DLehenbauer/econopet/docs/dev/PET/diagnostics.md

# Diagnostics

## Reference

* [cbm-burnin-tests](https://github.com/fachat/cbm-burnin-tests)
* [diagnostics.txt](https://www.zimmers.net/anonftp/pub/cbm/schematics/computers/pet/diagnostics.txt)
