DLehenbauer/econopet/docs/dev/timing.md

# Component Timing Reference

## W65C02S (CPU)

([Datasheet](https://www.westerndesigncenter.com/wdc/documentation/w65c02s.pdf))

| Symbol | Parameter | Min | Max | Units |
|---|---|-----|-----|---|
| tACC | Access Time |  70 | - | ns |
| tAH | Address Hold Time |  10 | - | ns |
| tADS | Address Setup Time | - |  40 | ns |
| tBVD | BE to Valid Data (1) | - |  30 | ns |
| tPWH | Clock Pulse Width High |  62 | - | ns |
| tPWL | Clock Pulse Width Low |  63 | - | ns |
| tCYC | Cycle Time (3) | 125 | - | ns |
| tF,tR  | Fall Time, Rise Time | - | 5 | ns |
| tPCH | Processor Control Hold Time |  10 | - | ns |
| tPCS | Processor Control Setup Time |  15 | - | ns |
| tDHR | Read Data Hold Time |  10 | - | ns |
| tDSR | Read Data Setup Time |  15 | - | ns |
| tMDS | Write Data Delay Time | - |  40 | ns |
| tDHW | Write Data Hold Time |  10 | - | ns |

Notes:

(1) BE to High Impedance State is not testable but should be the same amount of time as BE to Valid Data.

(3) Since this is a static design, the maximum cycle time could be infinite.

### Summary

Minimum Phi2 pulse width is high 62ns and low 63ns (tPWH, tPWL).

**Rising Phi2 edge triggers bus transfer:**

- BE must be asserted 45ns before rising Phi2 edge (tBVD + tDSR)
- DIN must be valid 15ns before rising Phi2 edge (tDSR)
- DIN must be held 10ns after rising Phi2 edge (tDHR)
- BE must be held 10ns after rising Phi2 edge (tDHR, tDHW)
- DOUT is valid within 40ns after rising Phi2 edge (tMDS)

**Falling Phi2 edge advances CPU to next state:**

- Previous ADDR, RWB, DOUT held 10ns after falling Phi2 edge (tAH, tDHW)
- Next ADDR, RWB, DOUT must be stable at least 40ns *before* the next rising Phi2 edge (tADS)
- Write data becomes valid within 40ns *after* that rising edge (tMDS)

**Other (design-derived):**

- At maximum clock rate, RAM has 70ns between ADDR stabilizing and the beginning of the read setup time (tACC).

## Soft-CPU Bus Timing

The physical PIA and VIA use `cpu_clock_o` as PHI2. The soft CPUs use separate
fabric clocks so their bus state does not advance until after the external
peripherals have observed falling PHI2 and completed their hold interval.

Within the 64-cycle, 64MHz arbiter frame:

| Event | Arbiter cycle | Purpose |
|---|---:|---|
| External PHI2 rises | 52 | Starts the physical peripheral transfer |
| CPU data strobe | 55 | External read or write data is guaranteed valid |
| External PHI2 falls | 60 | PIA and VIA latch the transfer |
| Soft 6809 Q falls | 60 | Samples synchronized interrupt inputs |
| Soft 6502 clock and 6809 E fall | 61 | Advances the selected soft CPU |

The 15.625ns interval from external PHI2 falling at cycle 60 to the soft-CPU
falling edge at cycle 61 exceeds the VIA's worst-case 10ns hold requirement.
Consequently, soft-CPU address, R/W, and write data remain stable without
adding bus latches.

`cpu_data_strobe` is itself registered. `main.sv` observes it on the following
system-clock edge, captures `cpu_data_q` for system-clock consumers, and raises
the delayed consumer strobe. That pulse also clocks `soft_cpu_data_q`, an
independent copy used only by the soft cores. This gives external data one
system-clock period to reach both capture registers. The soft-core copy remains
stable for five more system cycles before the selected core falls.

`EconoPET.sdc` models the short soft-core pulses with explicit generated-clock
edges. The first rising edge processes the initial `cycle_count` value 63, so
arbiter cycle 0 is processed on the second rising edge. SDC numbers every
source-clock transition (rise 1, fall 2, next rise 3), so arbiter cycle N
corresponds to source edge `2N+3`. The SDC also constrains the pin-to-capture
path to one system period. The delayed `cpu_data_strobe_q` pulse directly clocks
`soft_cpu_data_q` at cycle 56 and is declared as its generated launch clock.
STA can therefore derive the five-cycle setup and full-frame hold relationships
without a data-path exception. Keeping `cpu_data_q` on `sys_clock_i` separately
gives its consumers an ordinary one-cycle relationship. Remaining hold
adjustments are limited to edge-elastic READY/interrupt controls. The 6809's
IRQ sample register provides the first Q-domain synchronizer stage.

## W65C21N (PIA)

([Datasheet](https://www.westerndesigncenter.com/wdc/documentation/w65c21.pdf))

| Symbol | Parameter | Min | Max | Units |
|---|---|-----|-----|---|
| tCYC | PHI2 Cycle |  70 | - | ns |
| tC | PHI2 Pulse Width |  35 | - | ns |
| trc | PHI2 Rise Time | - | 5 | ns |
| tfc | PHI2 Fall Time | - | 5 | ns |
| tACR | Address Set-Up Time (read) | 8 | - | ns |
| tCAR | Address Hold Time (read) | 0 | - | ns |
| tPCR | Peripheral Data Setup Time |  10 | - | ns |
| tCDR | Data Bus Delay Time | - |  20 | ns |
| tHR | Data Bus Hold Time | 5 | - | ns |
| tACW | Address Set-Up Time (write) | 8 | - | ns |
| tCAW | Address Hold Time (write) | 0 | - | ns |
| tDCW | Data Bus Set-Up Time |  10 | - | ns |
| tHW | Data Bus Hold Time | 5 | - | ns |
| tCPW | Peripheral Data Delay Time | - |  20 | ns |

### Summary

- Minimum Phi2 pulse width is high 35ns and low 35ns (tCYC, tC)
- ADDR, RWD, CS2B must be stable at least 8ns before rising Phi2 (tACR, tACW) and may be released 0ns after falling Phi2 (tCAR, tCAW)
- Peripheral read data becomes valid within 20ns after rising Phi2 (tCDR) and is held 5ns after falling Phi2 (tHR)
- Peripheral write data must be set up 10ns before falling Phi2 (tDCW) and held 5ns after falling Phi2 (tHW)
- Peripheral-side data can appear within 20ns after rising Phi2 (tCPW)

## W65C22N (VIA)

([Datasheet](https://www.westerndesigncenter.com/wdc/documentation/w65c22.pdf))

| Symbol | Parameter | Min | Max | Units |
|---|---|-----|-----|---|
| tCYC | Cycle Time |  70 | - | ns |
| tPWH | Phase 2 Pulse Width High |  35 | - | ns |
| tPWL | Phase 2 Pulse Width Low |  35 | - | ns |
| tR,F | Phase 2 Transition | - | 5 | ns |
| tACR | CSx, RSx, RWB Setup - READ |  10 | - | ns |
| tCAR | CSx, RSx, RWB Hold (PHI2 falling edge) - READ |  10 | - | ns |
| tCDR | Data Bus Delay | - |  20 | ns |
| tHR | Data Bus Hold Time |  10 | - | ns |
| tPCR | Peripheral Data Setup |  10 | - | ns |
| tACW | CSx, RSx, RWB Setup - WRITE |  10 | - | ns |
| tCAW | CSx, RSx, RWB Hold (PHI2 falling edge) - WRITE | 10 | - | ns |
| tDCW | Data Bus Setup |  10 | - | ns |
| tHW | Data Bus Hold |  10 | - | ns |
| tCPW | Peripheral Data Delay | - | 250 | ns |

### Summary

- Minimum Phi2 pulse width is high 35ns and low 35ns (tPWH, tPWL)
- ADDR/CSx/RSx/RWB must be stable at least 10ns before rising Phi2 (tACR, tACW) and held 10ns after falling Phi2 (tCAR, tCAW).
- Peripheral read data becomes valid within 20ns after rising Phi2 (tCDR) and is held 10ns after falling Phi2 (tHR).
- Peripheral write data must be set up 10ns before falling Phi2 (tDCW) and held 10ns after falling Phi2 (tHW).
- Peripheral-side data can appear within ~250ns after rising Phi2 (tCPW).

## SN74LVC4245A (Level Shifter)

([Datasheet](https://www.ti.com/lit/ds/symlink/sn74lvc4245a.pdf))

Two SN74LVC4245A devices provide level shifting between the CPU and PIA/VIA:

- Address A0-A3: fixed direction from CPU to PIA/VIA (B to A), permanently enabled.
- Data D0-D7: bidirectional. DIR follows CPU RWB (read: A to B, write: B to A). /OE is asserted by the FPGA during decoded PIA/VIA accesses; otherwise the device is high-Z to avoid contention.

The timing values below bound propagation and enable/disable delays used when budgeting setup/hold margins for CPU-to-PIA/VIA transfers.

| Symbol | From | To | Min | Max  | Units |
|---|---|----|-----|---|---|
| tPHL | A | B  | 1 |  6.3 | ns |
| tPLH | A | B  | 1 |  6.7 | ns |
| tPHL | B | A  | 1 |  6.1 | ns |
| tPLH | B | A  | 1 |  5.0 | ns |
| tPZL | /OE  | A  | 1 |  9.0 | ns |
| tPZH | /OE  | A  | 1 | 10.0 | ns |
| tPZL | /OE  | B  | 1 | 10.3 | ns |
| tPZH | /OE  | B  | 1 |  9.8 | ns |
| tPLZ | /OE  | A  | 1 |  7.0 | ns |
| tPHZ | /OE  | B  | 1 |  5.8 | ns |
| tPLZ | /OE  | B  | 1 |  7.7 | ns |
| tPHZ | /OE  | B  | 1 |  7.8 | ns |

### Summary

- Propagation: A to B up to 6.7ns (tPLH A to B); B to A up to 6.1ns (tPHL B to A). Budget 6.7ns worst-case.
- Enable (/OE asserted): to B up to 10.3ns (tPZL /OE to B); to A up to 10.0ns (tPZH /OE to A).
- Disable (/OE deasserted): to B high-Z up to 7.8ns (tPHZ /OE to B); to A high-Z up to 7.0ns (tPLZ /OE to A). Budget 7.8ns worst-case.
- Turn-around: deassert /OE, wait >=7.8ns to reach high-Z, switch DIR, then re-assert /OE to avoid contention.

## AS6C1008-55PCN (SRAM)

([Datasheet](https://www.alliancememory.com/wp-content/uploads/AS6C1008_Mar_2023V1.2.pdf))

### Read Cycle

| Symbol | Parameter | Min | Max | Units |
|---|---|-----|-----|---|
| tRC | Read Cycle Time |  55 | - | ns |
| tAA | Address Access Time | - |  55 | ns |
| tACE | Chip Enable Access Time | - |  55 | ns |
| tOE | Output Enable Access Time | - |  30 | ns |
| tCLZ | Chip Enable to Output in Low-Z | - |  10 | ns |
| tOLZ | Output Enable to Output in Low-Z | - | 5 | ns |
| tCHZ | Chip Disable to Output in High-Z | - |  20 | ns |
| tOHZ | Output Disable to Output in High-Z | - |  20 | ns |
| tOH | Output Hold from Address Change |  10 | - | ns |

### Write Cycle

| Symbol | Parameter | Min | Max | Units |
|---|---|-----|-----|---|
| tWC | Write Cycle Time |  55 | - | ns |
| tAW | Address Valid to End of Write |  50 | - | ns |
| tAS | Address Setup Time | 0 | - | ns |
| tWP | Write Pulse Width |  45 | - | ns |
| tWR | Write Recovery Time | 0 | - | ns |
| tDW | Data to Write Time Overlap |  25 | - | ns |
| tDH | Data Hold from End of Write Time | 0 | - | ns |
| tOW | Output Active from End of Write | 5 | - | ns |
| tWHZ | Write to Output in High-Z | - |  20 | ns |

### Summary

- DOUT valid 55ns after coincident ADDR and OE: max(tAA, tOE, tOLZ).
- DOUT held 10ns after ADDR changes (tOH).
- DOUT returns to High-Z 20ns after OE deasserted (tOHZ).
- CE is permanently asserted, so tACE, tCLZ, tCHZ, and tCW are not relevant.
- Total write cycle time must be at least 55ns (tWC).
- ADDR must be valid 50ns before WE deasserts; no hold requirement (tAW, tWR = 0ns).
- DIN must be valid 25ns before WE deasserts; no hold requirement (tDW, tDH = 0ns).
- WE pulse width must be at least 45ns (tWP).
- OE is deasserted during writes, so tOW and tWHZ are not relevant.

## IS61WV1288EEBLL-10TLI (SRAM)

### Read Cycle

| Symbol | Parameter | Min | Max | Units |
|---|---|-----|-----|---|
| tRC | Read Cycle Time |  10 |  -  | ns |
| tAA | Address Access Time | - |  10 | ns |
| tOHA | Output Hold Time | 2.0 |  -  | ns |
| tACE | $\overline{CE}$ Access Time | - |  10 | ns |
| tDOE | $\overline{OE}$ Access Time | - | 4.5 | ns |
| tHZOE  | $\overline{OE}$ to High-Z Output | - | 4 | ns |
| tLZOE  | $\overline{OE}$ to Low-Z Output  | 0 | - | ns |
| tHZCE  | $\overline{CE}$ to High-Z Output | 0 | 4 | ns |
| tLZCE  | $\overline{CE}$ to Low-Z Output  | 3 | - | ns |
| tPU | Power Up Time | 0 | - | ns |
| tPD | Power Down Time | - |  10 | ns |

### Write Cycle

| Symbol | Parameter | Min | Max | Units |
|---|---|-----|-----|---|
| tWC | Write Cycle Time |  10 | - | ns |
| tSCE | $\overline{CE}$ to Write End | 8 | - | ns |
| tAW | Address Setup Time to Write End | 8 | - | ns |
| tHA | Address Hold from Write End | 0 | - | ns |
| tSA | Address Setup Time | 0 | - | ns |
| tPWE1  | $\overline{WE}$ Pulse Width | 8 | - | ns |
| tPWE2  | $\overline{WE}$ Pulse Width ($\overline{OE}$ = LOW) |  10 | - | ns |
| tSD | Data Setup to Write End | 6 | - | ns |
| tHD | Data Hold from Write End | 0 | - | ns |
| tHZWE  | $\overline{WE}$ LOW to High-Z Output | - | 5 | ns |
| tLZWE  | $\overline{WE}$ HIGH to Low-Z Output | 2 | - | ns |

### Summary

- DOUT valid 10ns after coincident ADDR and $\overline{CE}$ (tAA, tACE).
- DOUT valid 4.5ns after $\overline{OE}$ asserted (tDOE).
- DOUT held 2.0ns after ADDR changes (tOHA).
- DOUT returns to High-Z 4ns after $\overline{OE}$ or $\overline{CE}$ deasserted (tHZOE, tHZCE).
- Total write cycle time must be at least 10ns (tWC).
- ADDR must be valid 8ns before $\overline{WE}$ or $\overline{CE}$ deasserts (tAW).
- ADDR must be set up 0ns before $\overline{WE}$ or $\overline{CE}$ asserts (tSA).
- ADDR must be held 0ns after $\overline{WE}$ or $\overline{CE}$ deasserts (tHA).
- DIN must be valid 6ns before $\overline{WE}$ or $\overline{CE}$ deasserts (tSD).
- DIN must be held 0ns after $\overline{WE}$ or $\overline{CE}$ deasserts (tHD).
- $\overline{WE}$ pulse width must be at least 8ns (tPWE1) or 10ns if $\overline{OE}$ is LOW (tPWE2).
- $\overline{CE}$ must be asserted for at least 8ns before write end (tSCE).
