DLehenbauer/econopet/docs/dev/PET/roms.md

# ROMs

## Naming

 Common         | Geneology      | Generation | Level
----------------|----------------|------------|-----------------
 BASIC 1.0      | ROM 1.0        | Original   | Basic Level I
 BASIC 1.0R     | ROM 2.0        | Original   | Basic Level II  
 BASIC 2.0      | ROM 3.0        | Upgrade    | Basic Level III
 BASIC 4.0      | ROM 4.0        | 4.0        | Basic Level IV
 BASIC 4.0R     | ROM 4.1        | 4.0        | Basic Level IV

* [ROM Genealogy](http://penguincentral.com/retrocomputing/PET/petroms.pdf) is official Commodore documentation preserved by Ethan Dicks
* [ROM Genealogy](https://archive.org/details/commodore-newsletter-volume-1-number-10/page/31/mode/1up) is a subset of the above from Commodore Newsletter Vol 1, No 10 (1982)
* Jim Butterfield's [What Software Do I Have?](https://archive.org/details/cbm_magazine_index-interface/interface/1981/interface-13-198107/page/n10/mode/1up) article in Interface Magazine (July 1981)

## ROM 1.0

Early production PET 2001 units used MOS 6540 ROMs (28-pin).  Later revisions used 2316 ROMs (24-pin).

The 28-pin and 24-pin ROMs have different IC and part numbers, but their contents are identical.

Highlights:

* Arrays limited to 256 items
* IEEE-488 input not working
* Tape data files had potential problems
* No machine language monitor
* Screen output polls for vertical refresh to avoid "sparkle" (see [killerpoke.md](killerpoke.md))

Address | Location | 6540 IC# | 6540 Part# | 2316B IC# | 2316B Part# | CRC-32   | Checksum
--------|----------|----------|------------|-----------|-------------|----------|---------
  $C000 |    H1    | 6540-011 |  901439-01 | 2316B-01  |  901447-01  | a055e33a | AD?
  $D000 |    H2    | 6540-013 |  901439-02 | 2316B-03  |  901447-03  | d349f2d4 | 15?
  $E000 |    H3    | 6540-015 |  901439-03 | 2316B-05  |  901447-05  | 9e1c5cea | 60?
  $F000 |    H4    | 6540-016 |  901439-04 | 2316B-06  |  901447-06  | 661a814a | F5?
  $C800 |    H5    | 6540-012 |  901439-05 | 2316B-02  |  901447-02  | 69fd8a8f | 09?
  $D800 |    H6    | 6540-014 |  901439-06 | 2316B-04  |  901447-04  | 850544eb | 0E?
  $F800 |    H7    | 6540-018 |  901439-07 | 2316B-07  |  901447-07  | c4f47ad1 | 4A?
  N/A   |    A2    | 6540-010 |  901439-08 | 2316B-08  |  901447-08  | 54f32f45 | ?

### Keyboard (901447-05)

Graphics/QWERTY keyboard scanmap at $e75c:

```text
>C:e75c  3d 2e ff 03  3c 20 5b 12   =...< [.
>C:e764  2d 30 00 3e  ff 5d 40 00   -0.>.]@.
>C:e76c  2b 32 ff 3f  2c 4e 56 58   +2.?,NVX
>C:e774  33 31 0d 3b  4d 42 43 5a   31.;MBCZ
>C:e77c  2a 35 ff 3a  4b 48 46 53   *5.:KHFS
>C:e784  36 34 ff 4c  4a 47 44 41   64.LJGDA
>C:e78c  2f 38 ff 50  49 59 52 57   /8.PIYRW
>C:e794  39 37 5e 4f  55 54 45 51   97^OUTEQ
>C:e79c  14 11 ff 29  5c 27 24 22   ...)\'$"
>C:e7a4  1d 13 5f 28  26 25 23 21   .._(&%#!
```

### Vertical Refresh

To prevent sparkle, polls via VIA PB5 (pin 15) to wait for vertical refresh before writing to VRAM.

```txt
.C:e7ad  AD 40 E8    LDA $E840
.C:e7b0  29 20       AND #$20
.C:e7b2  D0 F9       BNE $E7AD
```

### Disk

There is a patch for H4 [here](https://hub.inktada.com/channel/rom1diskmagic) that fixes the issue with disk drives.

[Disassembly](https://www.zimmers.net/anonftp/pub/cbm/src/pet/rom-1.html)

## ROM 2.0

Highlights:

* Fixed bug limiting the dimensions of arrays.
* Corrects an intermittent bug in the edit software.
* Improves the garbage collection routines.

Identical to ROM 1.0 except H1 ($C000).

Address | Location | 6540 IC# | 6540 Part# | 2316B IC# | 2316B Part# | CRC-32   | Checksum
--------|----------|----------|------------|-----------|-------------|----------|---------
  $C000 | H1       | 6540-019 |  901439-09 | 2316B-09  |  901447-09  | 03cf16d0 | 19?

### PET 2001-8N (VICE)

The VICE roms are a binary concatenation of the ROMs indicated in the filenames:

ROM         | File                            | Length | CRC-32
------------|---------------------------------|--------|---------
Basic       | basic-1.901439-09-05-02-06.bin  |   8192 | aff78300
Edit        | edit-1-n.901439-03.bin          |   2048 | 9e1c5cea
Kernal      | kernal-1.901439-04-07.bin       |   4096 | f0186492
Characters  | characters-1.901447-08.bin      |   2048 | 54f32f45

## ROM 3.0

Highlights:

* Changed the banner ("***" -> "###")
* Fixed support for commodore disk system
* Adds machine language monitor
* Further improved garbage collection
* Re-arranged the zero-page and ROM entry points
* Adds ROM set for business keyboards
* New character ROM (swaps upper/lower case)
* Screen output polls for vertical refresh to avoid "sparkle" (see [killerpoke.md](killerpoke.md))

### PET 2001 / 30xx

The 24-pin BASIC and Kernal ROMs are 4KB.  The contents of H1-H3 are identical to the concatenation of H1/H5, H2/H6, H3/H7.
The 28-pin ROM upgrade set did not include a new character ROM.  Therefore, upper/lowercase continue to be swapped (like in BASIC 1-2).

Address | Location | 6540 IC# | 6540 Part# | CRC-32    | 2316B IC# | 2316B Part# | CRC-32   | Checksum
--------|----------|----------|------------|-----------|-----------|-------------|----------|---------
  $C000 | H1, D6   | 6540-020 |  901439-13 | 6aab64a5  |  2332-007 |   901465-01 | 63a7fe4a |    77
  $D000 | H2, D7   | 6540-022 |  901439-15 | 97f7396a  |  2332-008 |   901465-02 | ae4cb035 |    Cl
  $E000 | H3, D8   | 6540-024 |  901439-17 | e459ab32  | 2316B-011 |   901447-24 | e459ab32 |    C0
  $F000 | H4, D9   | 6540-025 |  901439-18 | 8745fc8a  |  2332-009 |   901465-03 | f02238e2 |    1D
  $C800 | H5       | 6540-021 |  901439-14 | a8f6ff4c  | -         |   -         | -        | -
  $D800 | H6       | 6540-023 |  901439-16 | 4cf8724c  | -         |   -         | -        | -
  $F800 | H7       | 6540-026 |  901439-19 | fd2c1f87  | -         |   -         | -        | -
  N/A   | A2, F10  | 6540-010 |  901439-08 | 54f32f45  | 2316B-004 |   901447-10 | d8408674 | ?

### PET 30xxB (Business Keyboard)

Business keyboard is identical except for editor ROM (D8).

Address | Location | IC#       | Part#     | CRC-32   | Checksum
--------|----------|-----------|-----------|----------|---------
  $E000 | D8       |2316B-024  | 901474-01 | 05db957e |    F3

### Scanmap (901474-01)

Business/QWERTY keyboard scanmap at $e6fb:

```text
>C:e6fb  50 e7 3a 03  39 36 33 df   P.:.963.
>C:e703  b1 2f ff 13  4d 20 58 12   ./..M X.
>C:e70b  b2 ff ff b0  2c 4e 56 5a   ....,NVZ
>C:e713  b3 00 ff ae  2e 42 43 00   .....BC.
>C:e71b  b4 db 4f 11  55 54 45 51   ..O.UTEQ
>C:e723  14 50 49 dc  59 52 57 89   .PI.YRW.
>C:e72b  b6 c0 4c 0d  4a 47 44 41   ..L.JGDA
>C:e733  b5 3b 4b dd  48 46 53 9b   .;K.HFS.
>C:e73b  b9 ff de b7  b0 37 34 31   .....741
>C:e743  ff ff 1d b8  2d 38 35 32   ....-852
```

Note that the first two table entries are an instruction. Presumably these keys are unpressable? (CTRL-V, CTRL-D)

```text
.C:e6fb  50 E7       BVC $E6E4
```

### PET 30xx (VICE)

The VICE roms are a binary concatenation of the ROMs indicated in the filenames:

ROM         | File                            | Length | CRC-32  
------------|---------------------------------|--------|---------
Basic       | basic-2.901465-01-02.bin        |   8192 | cf35e68b
Edit        | edit-2-n.901447-24.bin          |   2048 | e459ab32
Kernal      | kernal-2.901465-03.bin          |   4096 | f02238e2
Characters  | characters-2.901447-10.bin      |   2048 | d8408674

Business keyboard is identical to 30XX except for Edit rom.

ROM         | File                            | Length | CRC-32  
------------|---------------------------------|--------|---------
Edit        | edit-2-b.901474-01.bin          |   2048 | 05db957e

## ROM 4.0

Highlights:

* Added the disk commands and status variables
* Greatly improved the garbage collection
* Adds ROM set for 80 column displays

### PET 2001 & 40XX (Graphics Keyboard, NoCRTC)

Address | Location | IC#       | Part#     | CRC-32   | Checksum
--------|----------|-----------|-----------|----------|---------
  $9000 | D3       | -         | -         | -        | -
  $A000 | D4       | -         | -         | -        | -
  $B000 | D5       |  2332     | 901465-19 | 3a5f5721 |    B1?
  $C000 | D6       |  2332-059 | 901465-20 | 0fc17b9c |    C0
  $D000 | D7       |  2332-096 | 901465-21 | 36d91855 |    D0
  $E000 | D8       | 2316B-034 | 901447-29 | e5714d4c |    E0
  $F000 | D9       |  2332-075 | 901465-22 | cc5298a1 |    F0
  N/A   | F10      | 2316B-004 | 901447-10 | d8408674 | ?

### PET 2001 & 40XX (Business Keyboard, NoCRTC)

Business keyboard is identical except for D8.

Address | Location | IC#       | Part#     | CRC-32   | Checksum
--------|----------|-----------|-----------|----------|---------
  $E000 | D8       | 2316B-035 | 901474-02 | 75ff4af7 |    E0

### PET 40XX (CRTC, 60 Hz)

Same ICs as NoCRTC except UD7.

Address | Location | IC#       | Part#     | CRC-32   | Checksum
--------|----------|-----------|-----------|----------|---------
  $F000 | UD6      |  2332-075 | 901465-22 | cc5298a1 |    F0
  $E000 | UD7      |  2316B    | 901499-01 | 5f85bdf8 |    BC
  $D000 | UD8      |  2332-096 | 901465-21 | 36d91855 |    D0
  $C000 | UD9      |  2332-059 | 901465-20 | 0fc17b9c |    C0
  $B000 | UD10     |  2332     | 901465-19 | 3a5f5721 | ?
  $A000 | UD11     | -         | -         | -        | -
  $9000 | UD12     | -         | -         | -        | -
  N/A   | F10      | 2316B-004 | 901447-10 | d8408674 | ?

#### Graphics Scanmap (901498-01, 901499-01)

```text
>C:e73f  3d 2e 10 03  3c 20 5b 12   =...< [.
>C:e747  2d 30 00 3e  ff 5d 40 00   -0.>.]@.
>C:e74f  2b 32 ff 3f  2c 4e 56 58   +2.?,NVX
>C:e757  33 31 0d 3b  4d 42 43 5a   31.;MBCZ
>C:e75f  2a 35 ff 3a  4b 48 46 53   *5.:KHFS
>C:e767  36 34 ff 4c  4a 47 44 41   64.LJGDA
>C:e76f  2f 38 ff 50  49 59 52 57   /8.PIYRW
>C:e777  39 37 5e 4f  55 54 45 51   97^OUTEQ
>C:e77f  14 11 09 29  5c 27 24 22   ...)\'$"
>C:e787  1d 13 5f 28  26 25 23 21   .._(&%#!
```

#### CRTC Tables (901499-01)

Text Mode
```
>C:e7b1  31 28 29 0f  20 03 19 1d   1(). ...
>C:e7b9  00 09 00 00  10 00 00 00   ........
>C:e7c1  00 00                      ..
```

Graphics Mode
```
>C:e7c3  31 28 29 0f  28 05 19 21   1().(..!
>C:e7cb  00 07 00 00  10 00 00 00   ........
>C:e7d3  00 00                      ..
```

### PET 40XXB (CRTC, 60Hz, Business)

Business keyboard is identical to 40XX except for Edit rom.

ROM         | File                            | Length | CRC-32  
------------|---------------------------------|--------|---------
Edit        | edit-4-40-b-60Hz.ts.bin         |   2048 | 7a0e59ad

Below are the edit rom changes required for the business keyboard:

```patch
- .C:e55c  EA          NOP
- .C:e55d  EA          NOP
- .C:e55e  EA          NOP
- .C:e55f  EA          NOP
- .C:e560  EA          NOP
- .C:e561  EA          NOP
- .C:e562  EA          NOP
+ .C:e55c  AA          TAX
+ .C:e55d  08          PHP
+ .C:e55e  29 7F       AND #$7F
+ .C:e560  28          PLP
+ .C:e561  30 17       BMI $E57A
.C:e563  46 98       LSR $98
.C:e565  90 13       BCC $E57A
- .C:e567  EA          NOP
- .C:e568  EA          NOP
- .C:e569  EA          NOP
- .C:e56a  EA          NOP
- .C:e56b  EA          NOP
- .C:e56c  EA          NOP
- .C:e56d  EA          NOP
- .C:e56e  EA          NOP
- .C:e56f  EA          NOP
- .C:e570  EA          NOP
- .C:e571  EA          NOP
- .C:e572  EA          NOP
- .C:e573  EA          NOP
- .C:e574  EA          NOP
- .C:e575  EA          NOP
- .C:e576  EA          NOP
- .C:e577  EA          NOP
+ .C:e567  C9 2C       CMP #$2C
+ .C:e569  90 0D       BCC $E578
+ .C:e56b  C9 3C       CMP #$3C
+ .C:e56d  B0 09       BCS $E578
+ .C:e56f  E9 0F       SBC #$0F
+ .C:e571  C9 20       CMP #$20
+ .C:e573  B0 05       BCS $E57A
+ .C:e575  69 20       ADC #$20
+ .C:e577  2C 09 80    BIT $8009
```

```text
>C:e73f  16 04 3a 03  39 36 33 df   ..:.963.
>C:e747  b1 2f 15 13  4d 20 58 12   ./..M X.
>C:e74f  b2 10 0f b0  2c 4e 56 5a   ....,NVZ
>C:e757  b3 00 19 ae  2e 42 43 00   .....BC.
>C:e75f  b4 db 4f 11  55 54 45 51   ..O.UTEQ
>C:e767  14 50 49 dc  59 52 57 09   .PI.YRW.
>C:e76f  b6 c0 4c 0d  4a 47 44 41   ..L.JGDA
>C:e777  b5 3b 4b dd  48 46 53 9b   .;K.HFS.
>C:e77f  b9 06 de b7  b0 37 34 31   .....741
>C:e787  05 0e 1d b8  2d 38 35 32   ....-852
```

### PET 40XX (CRTC, 50Hz)

Identical except for UD7.  Scanmap at $e73f.

Address | Location | IC#       | Part#     | CRC-32   | Checksum
--------|----------|-----------|-----------|----------|---------
  $E000 | UD7      | 2316B     | 901498-01 | 3370e359 | ?

Below are the edit rom changes for 50 Hz.

```patch
- e455  20 ea ff   JSR UDTIM
+ e455  4c 2e e4   JMP $e42e
```

```patch
- e7b5  20         db 20h
+ e7b5  27         db 27h
- e7b6  03         db 3h
+ e7b6  00         db 0h
  e7b7  19         db 19h
- e7b8  1d         db 1Dh
+ e7b8  20         db 20h

- e7c7  28         db 28h
+ e7c7  31         db 31h
- e7c8  05         db 5h
+ e7c8  00         db 0h
  e7c9  19         db 19h
- e7ca  21         db 21h
+ e7ca  25         db 25h
```

```patch
- e7e4  bb         db BBh
+ e7e4  29         db 29h
```

#### CRTC Tables (901498-01)

Text Mode
```
>C:e7b1  31 28 29 0f  27 00 19 20   1().'.. 
>C:e7b9  00 09 00 00  10 00 00 00   ........
>C:e7c1  00 00
```

Graphics Mode
```
>C:e7c3  31 28 29 0f  31 00 19 25   1().1..%
>C:e7cb  00 07 00 00  10 00 00 00   ........
>C:e7d3  00 00                      ..
```

### PET 40XXB (CRTC, 50Hz, Business)

Business keyboard is identical to 40XX except for Edit rom.

ROM         | File                            | Length | CRC-32  
------------|---------------------------------|--------|---------
Edit        | edit-4-40-b-50Hz.ts.bin         |   2048 | 16fb070c

Below are the edit rom changes required for the business keyboard:

```patch
- .C:e55c  EA          NOP
- .C:e55d  EA          NOP
- .C:e55e  EA          NOP
- .C:e55f  EA          NOP
- .C:e560  EA          NOP
- .C:e561  EA          NOP
- .C:e562  EA          NOP
+ .C:e55c  AA          TAX
+ .C:e55d  08          PHP
+ .C:e55e  29 7F       AND #$7F
+ .C:e560  28          PLP
+ .C:e561  30 17       BMI $E57A
.C:e563  46 98       LSR $98
.C:e565  90 13       BCC $E57A
- .C:e567  EA          NOP
- .C:e568  EA          NOP
- .C:e569  EA          NOP
- .C:e56a  EA          NOP
- .C:e56b  EA          NOP
- .C:e56c  EA          NOP
- .C:e56d  EA          NOP
- .C:e56e  EA          NOP
- .C:e56f  EA          NOP
- .C:e570  EA          NOP
- .C:e571  EA          NOP
- .C:e572  EA          NOP
- .C:e573  EA          NOP
- .C:e574  EA          NOP
- .C:e575  EA          NOP
- .C:e576  EA          NOP
- .C:e577  EA          NOP
+ .C:e567  C9 2C       CMP #$2C
+ .C:e569  90 0D       BCC $E578
+ .C:e56b  C9 3C       CMP #$3C
+ .C:e56d  B0 09       BCS $E578
+ .C:e56f  E9 0F       SBC #$0F
+ .C:e571  C9 20       CMP #$20
+ .C:e573  B0 05       BCS $E57A
+ .C:e575  69 20       ADC #$20
+ .C:e577  2C 09 80    BIT $8009
```

```text
>C:e73f  16 04 3a 03  39 36 33 df   ..:.963.
>C:e747  b1 2f 15 13  4d 20 58 12   ./..M X.
>C:e74f  b2 10 0f b0  2c 4e 56 5a   ....,NVZ
>C:e757  b3 00 19 ae  2e 42 43 00   .....BC.
>C:e75f  b4 db 4f 11  55 54 45 51   ..O.UTEQ
>C:e767  14 50 49 dc  59 52 57 09   .PI.YRW.
>C:e76f  b6 c0 4c 0d  4a 47 44 41   ..L.JGDA
>C:e777  b5 3b 4b dd  48 46 53 9b   .;K.HFS.
>C:e77f  b9 06 de b7  b0 37 34 31   .....741
>C:e787  05 0e 1d b8  2d 38 35 32   ....-852
```

### PET 80XX (CRTC, 60Hz)

Identical except for UD7.

Address | Location | IC#       | Part#     | CRC-32   | Checksum
--------|----------|-----------|-----------|----------|---------
  $E000 | UD7      | 2316B-041 | 901474-03 | 5674dd5e | ?

#### CRTC Tables (901474-03)

Text Mode

```text
>C:e72a  31 28 29 0f  20 03 19 1d   1(). ...
>C:e732  00 09 00 00  10 00 00 00   ........
>C:e73a  00 00                      ..
```

Graphics Mode

```text
>C:e73c  31 28 29 0f  28 05 19 21   1().(..!
>C:e744  00 07 00 00  10 00 00 00   ........
>C:e74c  00 00                      ..
```

#### Business Scanmap (901474-03, 901474-04)

```text
>C:e6d1  16 04 3a 03  39 36 33 df   ..:.963.
>C:e6d9  b1 2f 15 13  4d 20 58 12   ./..M X.
>C:e6e1  b2 10 0f b0  2c 4e 56 5a   ....,NVZ
>C:e6e9  b3 00 19 ae  2e 42 43 00   .....BC.
>C:e6f1  b4 db 4f 11  55 54 45 51   ..O.UTEQ
>C:e6f9  14 50 49 dc  59 52 57 09   .PI.YRW.
>C:e701  b6 c0 4c 0d  4a 47 44 41   ..L.JGDA
>C:e709  b5 3b 4b dd  48 46 53 9b   .;K.HFS.
>C:e711  b9 06 de b7  b0 37 34 31   .....741
>C:e719  05 0e 1d b8  2d 38 35 32   ....-852
```

Below are the edit rom changes required for the graphics keyboard:

```patch
- .C:e545  AA          TAX
- .C:e546  08          PHP
- .C:e547  29 7F       AND #$7F
- .C:e549  28          PLP
- .C:e54a  30 17       BMI $E563
+ .C:e545  EA          NOP
+ .C:e546  EA          NOP
+ .C:e547  EA          NOP
+ .C:e548  EA          NOP
+ .C:e549  EA          NOP
+ .C:e54A  EA          NOP
+ .C:e54B  EA          NOP
.C:e54c  46 98       LSR $98
.C:e54e  90 13       BCC $E563
- .C:e550  C9 2C       CMP #$2C
- .C:e552  90 0D       BCC $E561
- .C:e554  C9 3C       CMP #$3C
- .C:e556  B0 09       BCS $E561
- .C:e558  E9 0F       SBC #$0F
- .C:e55a  C9 20       CMP #$20
- .C:e55c  B0 05       BCS $E563
- .C:e55e  69 20       ADC #$20
- .C:e560  2C 09 80    BIT $8009
+ .C:e550  EA          NOP
+ .C:e551  EA          NOP
+ .C:e552  EA          NOP
+ .C:e553  EA          NOP
+ .C:e554  EA          NOP
+ .C:e555  EA          NOP
+ .C:e556  EA          NOP
+ .C:e557  EA          NOP
+ .C:e558  EA          NOP
+ .C:e559  EA          NOP
+ .C:e55a  EA          NOP
+ .C:e55b  EA          NOP
+ .C:e55c  EA          NOP
+ .C:e55d  EA          NOP
+ .C:e55e  EA          NOP
+ .C:e55f  EA          NOP
+ .C:e560  EA          NOP
```

```
>C:e6d1  3d 2e 10 03  3c 20 5b 12   =...< [.
>C:e6d9  2d 30 00 3e  ff 5d 40 00   -0.>.]@.
>C:e6e1  2b 32 ff 3f  2c 4e 56 58   +2.?,NVX
>C:e6e9  33 31 0d 3b  4d 42 43 5a   31.;MBCZ
>C:e6f1  2a 35 ff 3a  4b 48 46 53   *5.:KHFS
>C:e6f9  36 34 ff 4c  4a 47 44 41   64.LJGDA
>C:e701  2f 38 ff 50  49 59 52 57   /8.PIYRW
>C:e709  39 37 5e 4f  55 54 45 51   97^OUTEQ
>C:e711  14 11 09 29  5c 27 24 22   ...)\'$"
>C:e719  1d 13 5f 28  26 25 23 21   .._(&%#!
```

### PET 80XX (CRTC, 50Hz)

Identical except for UD7.  Scanmap at $e6d1.

Address | Location | IC#       | Part#     | CRC-32   | Checksum
--------|----------|-----------|-----------|----------|---------
  $E000 | UD7      | 2316B-059 | 901474-04 | c1ffca3a | ?

#### CRTC Tables (901474-04)

Text Mode
```
>C:e72a  3f 28 32 08  20 10 19 1d   ?(2. ...
>C:e732  00 08 00 00  10 00 00 00   ........
>C:e73a  00 00                      ..
```

Graphics Mode
```
>C:e73c  3f 28 32 08  24 11 19 20   ?(2.$.. 
>C:e744  00 07 00 00  10 00 00 00   ........
>C:e74c  00 00                      ..
```

## ROM 4.1

ROM 4.1 is identical to ROM 4.0 except for D5/UD10.

Address | Location | IC#       | Part#     | CRC-32   | Checksum
--------|----------|-----------|-----------|----------|---------
  $B000 | D5       |  2332-120 | 901465-23 | ae3deac0 |    B0

### PET 40xx (VICE)

The VICE roms are a binary concatenation of the ROMs indicated in the filenames:

ROM         | File                            | Length | CRC-32  
------------|---------------------------------|--------|---------
Basic       | basic-4.901465-23-20-21.bin     |  12288 | 2a940f0a
Edit        | edit-4-40-n-50Hz.901498-01.bin  |   2048 | 3370e359
Kernal      | kernal-4.901465-22.bin          |   4096 | cc5298a1
Characters  | characters-2.901447-10.bin      |   2048 | d8408674

The Basic ROM is a concatenation of:

* 901465-23 ($B***)
* 901465-20 ($C***)
* 901465-21 ($D***)

## 8296

ROM          | Address | Location | IC#       | Part#     | CRC-32   | Checksum
-------------|-------- |----------|-----------|-----------|----------|---------
Option       | $9000   | UE10     | -         | -         | -        | -
Option       | $A000   | UE9      | -         | -         | -        | -
Editor ASCII | -       | UE8      | -         | 901474-04 | -        | -
Editor DIN   | -       | UE8      | -         | 324243-01 | -        | -
Basic/Kernal | $B000   | UE7      | -         | 324746-01 | -        | -
Char ASCII   | -       | UE5      | -         | 901447-10 | -        | -
Char DIN     | -       | UE5      | -         | 324242-01 | -        | -

The Basic/Kernal ROM is a concatenation of:

* 901465-23 ($B***)
* 901465-20 ($C***)
* 901465-21 ($D***)
* 901465-22 ($F***)

## 8296D

Same as 8296, except for the editor ROM (UE8)?

ROM          | Address | Location | IC#       | Part#      | CRC-32   | Checksum
-------------|-------- |----------|-----------|------------|----------|---------
Editor ASCII | -       | UE8      | -         | 324243-02B | -        | -
Editor DIN   | -       | UE8      | -         | 324243-03  | -        | -

## Appendix A: 6540 ROMs (28-pin)

Some static PET units use 28-pin 6540 ROMs instead of the 24-pin 23xx ROMs standardized
on by Commodore in later models.

Mainboard | ROMs  | RAM
----------|-------|-----
320008    | 6540  | 6550
320081    | 2316B | 6550
320132    | 6540  | 2114
320137    | 2316B | 2114

The content of the 6540 ROMs are identical to the their 23xx counterparts.

## Appendix B: ROM Table

Model       | Type                    | Function                                       | Part#      | Size | Address   | IC        | Version | Revision | Copyright | CRC-32     | Code  
------------|-------------------------|------------------------------------------------|------------|------|-----------|-----------|---------|----------|-----------|------------|-------
CBM 30xx    | Character (8 Scanlines) | PET Character (Basic 3/4) (F10)                | 901447-10  | 2KB  | -         | 2316B-004 | -       | -        | -         | 0xd8408674 | BINARY
CBM 30xx    | Character (8 Scanlines) | PET Character (Swedish) (F10)                  | 901447-14  | 2KB  | -         | 2316B     | -       | -        | -         | 0x48c77d29 | BINARY
CBM 30xx    | Diagnostic              | Commodore PET ROM Tester                       | 901447-18  | 2KB  | 9800-9FFF | 2316B     | -       | -        | -         | 0x081c7aad | 6502  
CBM 30xx    | Basic                   | PET Basic 3 $C0 (H1)                           | 901447-20  | 2KB  | C000-C7FF | 2316B-007 | 3       | -        | -         | 0x6aab64a5 | 6502  
CBM 30xx    | Basic                   | PET Basic 3 $C (D6)                            | 901465-01  | 4KB  | C000-CFFF | 2332-007  | 3       | -        | -         | 0x63a7fe4a | 6502  
CBM 30xx    | Basic                   | PET Basic 3 $C8 (H5)                           | 901447-21  | 2KB  | C800-CFFF | 2316B-008 | 3       | -        | -         | 0xa8f6ff4c | 6502  
CBM 30xx    | Basic                   | PET Basic 3 $D0 (H2)                           | 901447-22  | 2KB  | D000-D7FF | 2316B-009 | 3       | -        | -         | 0x97f7396a | 6502  
CBM 30xx    | Basic                   | PET Basic 3 $D (D7)                            | 901465-02  | 4KB  | D000-DFFF | 2332-008  | 3       | -        | -         | 0xae4cb035 | 6502  
CBM 30xx    | Basic                   | PET Basic 3 $D8 (H6)                           | 901447-23  | 2KB  | D800-DFFF | 2316B     | 3       | -        | -         | 0x4cf8724c | 6502  
CBM 30xx    | Editor                  | PET Edit 3 40 B NoCRTC (D8)                    | 901474-01  | 2KB  | E000-E7FF | 2316B     | 3       | -        | -         | 0x05db957e | 6502  
CBM 30xx    | Editor                  | PET Edit 3 40 N NoCRTC (D8, H3)                | 901447-24  | 2KB  | E000-E7FF | 2316B-011 | 3       | -        | -         | 0xe459ab32 | 6502  
CBM 30xx    | Kernal                  | PET Basic 3 $F0 (H4)                           | 901447-25  | 2KB  | F000-F7FF | 2316B-012 | 3       | -        | -         | 0x8745fc8a | 6502  
CBM 30xx    | Kernal                  | PET Kernal 3 $F (D9)                           | 901465-03  | 4KB  | F000-FFFF | 2332-009  | 3       | -        | -         | 0xf02238e2 | 6502  
CBM 30xx    | Kernal                  | PET Basic 3 $F8 (H7)                           | 901447-26  | 2KB  | F800-FFFF | 2316B-013 | 3       | -        | -         | 0xfd2c1f87 | 6502  
CBM 40xx    | Basic                   | PET Basic 4 $B (D5, UD10)                      | 901465-19  | 4KB  | B000-BFFF | 2332      | 4       | -        | -         | 0x3a5f5721 | 6502  
CBM 40xx    | Basic                   | PET Basic 4 $C (D6, UD9)                       | 901465-20  | 4KB  | C000-CFFF | 2332-059  | 4       | -        | -         | 0x0fc17b9c | 6502  
CBM 40xx    | Basic                   | PET Basic 4 $D (D7, UD8)                       | 901465-21  | 4KB  | D000-DFFF | 2332-096  | 4       | -        | -         | 0x36d91855 | 6502  
CBM 40xx    | Editor                  | PET Edit 4 40 B NoCRTC (D8)                    | 901474-02  | 2KB  | E000-E7FF | 2316B-035 | 4       | -        | -         | 0x75ff4af7 | 6502  
CBM 40xx    | Editor                  | PET Edit 4 40 N CRTC 50Hz (UD7)                | 901498-01  | 2KB  | E000-E7FF | 2316B     | 4       | -        | -         | 0x3370e359 | 6502  
CBM 40xx    | Editor                  | PET Edit 4 40 N CRTC 50Hz (UD7)                | editor.bin | 2KB  | E000-E7FF | 2716      | 4       | -        | -         | 0xeb9f6e75 | 6502  
CBM 40xx    | Editor                  | PET Edit 4 40 N CRTC 60Hz (UD7)                | 901499-01  | 2KB  | E000-E7FF | 2316B     | 4       | -        | -         | 0x5f85bdf8 | 6502  
CBM 40xx    | Editor                  | PET Edit 4 40 N NoCRTC (D8)                    | 901447-29  | 2KB  | E000-E7FF | 2316B-034 | 4       | -        | -         | 0xe5714d4c | 6502  
CBM 40xx    | Editor                  | PET Edit 4 CRTC 60Hz (PET 9")                  | 970150-07  | 2KB  | E000-E7FF | 2716      | 4       | -        | -         | -          | 6502  
CBM 40xx    | Kernal                  | PET Kernal 4 $F (D9, UD6)                      | 901465-22  | 4KB  | F000-FFFF | 2332-075  | 4       | -        | -         | 0xcc5298a1 | 6502  
CBM 40xx    | Basic                   | PET Basic 4.1 $B (D5, UD10)                    | 901465-23  | 4KB  | B000-BFFF | 2332-120  | 4.1     | -        | -         | 0xae3deac0 | 6502  
CBM 80xx    | Software                | COMTEXT (UD12)                                 | 324482-03  | 4KB  | 9000-9FFF | 2532      | -       | -        | -         | 0xcc01c40a | 6502  
CBM 80xx    | -                       | Diagnostics 80 Col                             | 901481-01  | 4KB  | F000-FFFF | 2332      | -       | -        | -         | 0x24e4a616 | 6502  
CBM 80xx    | Expansion               | PET High Speed Graphik Rev 1B                  | 324381-01B | 4KB  | A000-AEFF | 2332      | -       | 1B       | -         | 0xc8e3bff9 | 6502  
CBM 80xx    | Editor                  | PET Edit 4 80 B CRTC 50Hz (UD7)                | 901474-04  | 2KB  | E000-E7FF | 2316B-059 | 4       | -        | -         | 0xc1ffca3a | 6502  
CBM 80xx    | Editor                  | PET Edit 4 80 B CRTC 60Hz (UD7)                | 901474-03  | 2KB  | E000-E7FF | 2316B-041 | 4       | -        | -         | 0x5674dd5e | 6502  
CBM 80xx    | Editor                  | PET Edit 4 80 CRTC 60Hz (UD7)                  | 901499-03  | 2KB  | E000-E7FF | 2316B     | 4       | -        | -         | -          | 6502  
CBM 80xx CR | Basic                   | PET Basic 4 & Kernal 4 (UE7)                   | 324746-01  | 16KB | B000-FFFF | 23128-632 | 4       | -        | 1983      | 0x03a25bb4 | 6502  
CBM 80xx CR | Editor                  | PET Edit 4 80 8296 DIN 50Hz (UE8)              | 324243-01  | 4KB  | E000-EFFF | 2532      | 4       | -        | 1982      | 0x4000e833 | 6502  
CBM 8296    | Character (8 Scanlines) | PET Character DIN (UC5)                        | 324242-01  | 4KB  | 4KB       | 2532      | -       | -        | -         | Check      | BINARY
CBM 8296    | Basic                   | PET Basic 4 High & Kernal 4                    | 324878-02HI | 8KB | B000-FFFF | 2764      | 4.0     | -        | -         | Check      | 6502
CBM 8296    | Basic                   | PET Basic 4 Low                                | 324878-01LO | 8KB | C000-DFFF | 2764      | 4.0     | -        | -         | Check      | 6502
CBM 8296    | Editor                  | PET Edit 4 80 8296 Execudesk                   | execudesk  | 4KB  | E000-EFFF | 2532      | 4.0     | -        | -         | Check      | 6502
CBM 8296    | Editor                  | PET Edit 4 80 8296 Execudesk                   | execudesk_86-02 | 4KB | E000-EFFF | 2532  | 4.0     | -        | -         | Check      | 6502
CBM 8296 D  | Editor                  | PET Edit 4 80 8296D DIN (UE8)                  | 324243-03  | 4KB  | E000-EFFF | 2532      | -       | -        | 1982      | Check      | 6502
CBM 8296 D  | Editor                  | PET Edit 4 80 8296D DIN (UE8)                  | 324243-04  | 4KB  | E000-EFFF | 2332      | 4.0     | -        | 1982      | Check      | 6502
CBM 8296 D  | Editor                  | PET Edit 4 80 B 8296 ASCII (UE8)               | 324243-02B | 4KB  | E000-EFFF | 2532      | 4.0     | -        | -         | Check      | 6502
PET 2001    | -                       | -                                              | 901447-16  | 2KB  | -         | 2316B     | -       | -        | -         | -          | -
PET 2001    | Character (8 Scanlines) | PET Character (Basic 1/2) (A2)                 | 901439-08  | 2KB  | -         | 6540-010  | -       | -        | -         | 0x54f32f45 | BINARY
PET 2001    | Character (8 Scanlines) | PET Character (Basic 1/2) (F10, A2)            | 901447-08  | 2KB  | -         | 2316B-08  | -       | -        | -         | 0x54f32f45 | BINARY
PET 2001    | Character (8 Scanlines) | PET Character Japanese                         | 901447-12  | 2KB  | -         | 2316B     | -       | -        | -         | 0x2c9c8d89 | BINARY
PET 2001    | Diagnostic              | Diagnostic Clip                                | 901447-30  | 2KB  | 9800-9FFF | 2316B     | -       | -        | -         | 0x73fe1901 | 6502  
PET 2001    | Basic                   | PET Col80 $B                                   | 901465-15  | 4KB  | B000-BFFF | 2332      | -       | -        | -         | -          | 6502  
PET 2001    | Basic                   | PET Col80 $C                                   | 901465-16  | 4KB  | C000-CFFF | 2332      | -       | -        | -         | -          | 6502  
PET 2001    | Basic                   | PET Col80 $D                                   | 901465-17  | 4KB  | D000-DFFF | 2332      | -       | -        | -         | -          | 6502  
PET 2001    | Kernal                  | -                                              | 901465-04  | 4KB  | F000-FFFF | 2332      | -       | -        | -         | -          | 6502  
PET 2001    | Kernal                  | PET Col80 $F                                   | 901465-18  | 4KB  | F000-FFFF | 2332      | -       | -        | -         | -          | 6502  
PET 2001    | Basic                   | PET Basic 1 $C0 (H1)                           | 901447-01  | 2KB  | C000-C7FF | 2316B-01  | 1       | -        | -         | 0xa055e33a | 6502  
PET 2001    | Basic                   | PET Basic 1 $C0 (H1)                           | 901439-01  | 2KB  | C000-C7FF | 6540-011  | 1       | -        | -         | 0xa055e33a | 6502  
PET 2001    | Basic                   | PET Basic 1/2 $C8 (H5)                         | 901447-02  | 2KB  | C800-CFFF | 2316B-02  | 1       | -        | -         | 0x69fd8a8f | 6502  
PET 2001    | Basic                   | PET Basic 1/2 $C8 (H5)                         | 901439-05  | 2KB  | C800-CFFF | 6540-012  | 1       | -        | -         | 0x69fd8a8f | 6502  
PET 2001    | Basic                   | PET Basic 1/2 $D0 (H2)                         | 901447-03  | 2KB  | D000-D7FF | 2316B-03  | 1       | -        | -         | 0xd349f2d4 | 6502  
PET 2001    | Basic                   | PET Basic 1/2 $D0 (H2)                         | 901439-02  | 2KB  | D000-D7FF | 6540-013  | 1       | -        | -         | 0xd349f2d4 | 6502  
PET 2001    | Basic                   | PET Basic 1/2 $D8 (H6)                         | 901447-04  | 2KB  | D800-DFFF | 2316B-04  | 1       | -        | -         | 0x850544eb | 6502  
PET 2001    | Basic                   | PET Basic 1/2 $D8 (H6)                         | 901439-06  | 2KB  | D800-DFFF | 6540-014  | 1       | -        | -         | 0x850544eb | 6502  
PET 2001    | Editor                  | PET Basic 1/2 $E0 (H3)                         | 901447-05  | 2KB  | E000-E7FF | 2316B-05  | 1       | -        | -         | 0x9e1c5cea | 6502  
PET 2001    | Editor                  | PET Basic 1/2 $E0 (H3)                         | 901439-03  | 2KB  | E000-E7FF | 6540-015  | 1       | -        | -         | 0x9e1c5cea | 6502  
PET 2001    | Kernal                  | PET Basic 1/2 $F0 (H4)                         | 901447-06  | 2KB  | F000-F7FF | 2316B-06  | 1       | -        | -         | 0x661a814a | 6502  
PET 2001    | Kernal                  | PET Basic 1/2 $F0 (H4)                         | 901439-04  | 2KB  | F000-F7FF | 6540-016  | 1       | -        | -         | 0x661a814a | 6502  
PET 2001    | Kernal                  | PET Basic 1/2 $F8 (H7)                         | 901447-07  | 2KB  | F800-FFFF | 2316B-07  | 1       | -        | -         | 0xc4f47ad1 | 6502  
PET 2001    | Kernal                  | PET Basic 1/2 $F8 (H7)                         | 901439-07  | 2KB  | F800-FFFF | 6540-018  | 1       | -        | -         | 0xc4f47ad1 | 6502  
PET 2001    | Basic                   | PET Basic 2 $C0 (H1)                           | 901447-09  | 2KB  | C000-C7FF | 2316B-09  | 2       | -        | -         | 0x03cf16d0 | 6502  
PET 2001    | Basic                   | PET Basic 2 $C0 (H1)                           | 901439-09  | 2KB  | C000-C7FF | 6540-019  | 2       | -        | -         | 0x03cf16d0 | 6502  
PET 2001    | Basic                   | PET Basic 3 $C0 (H1)                           | 901439-13  | 2KB  | C000-C7FF | 6540-020  | 3       | -        | -         | 0x6aab64a5 | 6502  
PET 2001    | Basic                   | PET Basic 3 $C8 (H5)                           | 901439-14  | 2KB  | C800-CFFF | 6540-021  | 3       | -        | -         | 0xa8f6ff4c | 6502  
PET 2001    | Basic                   | PET Basic 3 $D0 (H2)                           | 901439-15  | 2KB  | D000-D7FF | 6540-022  | 3       | -        | -         | 0x97f7396a | 6502  
PET 2001    | Basic                   | PET Basic 3 $D8 (H6)                           | 901439-16  | 2KB  | D800-DFFF | 6540-023  | 3       | -        | -         | 0x4cf8724c | 6502  
PET 2001    | Editor                  | PET Basic 3 $E0 (H3)                           | 901439-17  | 2KB  | E000-E7FF | 6540-024  | 3       | -        | -         | 0xe459ab32 | 6502  
PET 2001    | Kernal                  | PET Basic 3 $F0 (H4)                           | 901439-18  | 2KB  | F000-F7FF | 6540-025  | 3       | -        | -         | 0x8745fc8a | 6502  
PET 2001    | Kernal                  | PET Basic 3 $F8 (H7)                           | 901439-19  | 2KB  | F800-FFFF | 6540-026  | 3       | -        | -         | 0xfd2c1f87 | 6502  

## Reference

* [Files](https://www.zimmers.net/anonftp/pub/cbm/firmware/computers/pet/index.html)
* Disassembly
  * [Original Commodore Sources](https://github.com/mist64/cbmsrc)
  * [Basic, Editor, and Kernal from 8032 4.0 CRTC 60Hz Business](https://www.zimmers.net/anonftp/pub/cbm/src/pet/pet_rom4_disassembly.txt)
  * [Editor from 4032 4.0 CRTC 60Hz Graphics](https://www.zimmers.net/anonftp/pub/cbm/firmware/computers/pet/edit-4-40-n-60hz-901499-01.dis.txt)
  * [SJGray's Disassemblies](https://github.com/sjgray/cbm-edit-rom/tree/master/disassemblies)
* [Memory Map](https://www.commodore.ca/manuals/pdfs/commodore_pet_memory_map.pdf)
* [PET-Interfaces.txt](https://www.zimmers.net/anonftp/pub/cbm/firmware/computers/pet/PET-Interfaces.txt) by William Levak
* Genealogy
  * The Official Commodore ROM Genealogy [1](https://archive.org/details/commodore-newsletter-volume-1-number-10/page/30/mode/2up) [2](http://penguincentral.com/retrocomputing/PET/petroms.pdf) [3](https://www.zimmers.net/anonftp/pub/cbm/firmware/computers/pet/Commodore%20ROM%20Genealogy.pdf)
* [DIAG.TXT](https://zimmers.net/anonftp/pub/cbm/firmware/misc/petdiag/petdiag.zip)
* [PET-Parts.txt](https://www.zimmers.net/anonftp/pub/cbm/firmware/computers/pet/PET-parts.txt) by William Levak
* [README](https://www.zimmers.net/anonftp/pub/cbm/firmware/computers/pet/README) by Olaf Seibert
* [README.also](https://www.zimmers.net/anonftp/pub/cbm/firmware/computers/pet/README.also) by William Levak
* [Hash Codes](http://mhv.bplaced.net/cbmroms/cbmroms.php)
* [Keyscan Maps](https://github.com/sjgray/cbm-edit-rom/blob/master/keyboard-tables1.asm)
* [Jim Butterfield](https://archive.org/details/cbm_magazine_index-interface/interface/1981/interface-13-198107/page/n9/mode/2up)
* Basic 1/2 IEEE Bug:
  * [Fachat's Notes](https://www.softwolves.com/arkiv/cbm-hackers/24/24293.html)
  * [PET 2001 IEEE patch from VICE](https://lc64.blogspot.com/2018/02/pet2001-basic1-ieee-patch-from-vice.html)
  * [Rom1 Disk Magic](https://hub.inktada.com/channel/rom1diskmagic)
* 8296
  * [8296D Service Manual (DE)](https://ia903406.us.archive.org/31/items/manual_8296D_SM_COMMODORE_DE/8296D_SM_COMMODORE_DE_text.pdf)
  * [André Fachat's Notes](https://zimmers.net/anonftp/pub/cbm/firmware/computers/pet/8296/edit-50hz-324243-02b.txt)

## Tools

* [cbmsymbols](https://github.com/ethandicks/cbmsymbols/)
* [romcheck](https://github.com/fachat/cbm-burnin-tests/blob/main/romcheck.c)
* [Ghidra](https://github.com/NationalSecurityAgency/ghidra)
  * `winget install Microsoft.OpenJDK.21`
* [WFDis](https://www.white-flame.com/wfdis/)
