DLehenbauer/econopet/docs/dev/PET/joystick.md

# Joystick

Known standards:
* SNES Adapter
* Coyote Electronics ("Best of the PET Gazette", pg. 44)
    * Consistent with pet_joystick.txt
    * Consistent with Tynemouth adapter
* Chuck Johnson ("Best ef the PET Gazette", pg. 43)
* Space Invaders+

Controller Port | Co Port 1  | Co Port2   | CJ Port1 | CJ Port2 | Space Invaders
----------------|------------|------------|----------|----------|----------------
1: Up           | PA0        | PA4        |  PA3     | PA7      | PA2
2: Down         | PA1        | PA5        |  PA2     | PA6      | PA3
3: Left         | PA2        | PA6        |  PA1     | PA5      | PA0
4: Right        | PA3        | PA7        |  PA0     | PA4      | PA1
6: Fire         | PA0 & 1    | PA4 & 5    |  PA2 & 3 | PA6 & 7  | PA5
7: +5V          |            |            |          |          |
8: GND          |            |            |          |          |

## Reference

* [snes_adapter.zip](https://www.zimmers.net/anonftp/pub/cbm/documents/projects/interfaces/snes_adapter.zip)
* [Tynemouth Dual 9 way D Joystick for PET Userport V2.0](https://www.sellmyretro.com/uploaded/img/Tynemouth%20Dual%209%20way%20D%20Joystick%20for%20PET%20Userport%20V2.0.pdf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)
* [Best of the PET Gazette](https://ia803407.us.archive.org/1/items/bestofpetgazette00petg/bestofpetgazette00petg.pdf)
* [pet_joystick.txt](https://www.zimmers.net/anonftp/pub/cbm/documents/projects/interfaces/pet_joystick.txt)
