DLehenbauer/econopet/fw/src/ieee/ieee_drive.c

// SPDX-License-Identifier: CC0-1.0
// https://github.com/dlehenbauer/econopet

#include "pch.h"
#include "ieee_drive.h"

#include <stdio.h>
#include <string.h>

#if defined(PICO_RP2040)
#include "pico/time.h"
#endif

#include "diag/log/log.h"
#include "diskimage.h"
#include "driver.h"
#include "fatal.h"
#include "hardware_contract.h"
#include "ieee_protocol.h"
#include "sd/sd.h"

#define DEV_ADDR 8

// The fabric answers devices 8 through 11, each a dual-drive unit. Mount
// slot = unit * DRIVES_PER_UNIT + drive, so slots 0/1 map to device 8 and
// slots 6/7 map to device 11.
#define NUM_UNITS       4
#define DRIVES_PER_UNIT 2
#define NUM_DRIVES      (NUM_UNITS * DRIVES_PER_UNIT)

static void ieee_ctrl_write(uint8_t value) {
    spi_write_at(ECONOPET_WB_IEEE_CTRL_ADDR, value);
}

// ----------------------------------------------------------------------------
// Disk images
// ----------------------------------------------------------------------------

typedef struct {
    FILE* file;
    diskimage_t image;
    bool present;
    char name[SD_PATH_MAX];  // image path currently "inserted"
} drive_t;

static drive_t drives[NUM_DRIVES];
static bool emulation_enabled = false;

typedef enum {
    drive_model_4040,
    drive_model_8050,
} drive_model_t;

// ----------------------------------------------------------------------------
// REL chain cache (built at mount time)
// ----------------------------------------------------------------------------
// The Super-OS/9 loader bounds drive latency with a counted DAV poll
// (~1.25s at 1MHz), so chains are prebuilt at mount. Links never change
// after mount (record writes reuse existing sectors).
#define CHAIN_CACHE_SLOTS 4

typedef struct {
    bool valid;
    uint8_t track, sector;              // chain start track/sector = cache key
    diskchain_t chain;
} chain_cache_entry_t;

static chain_cache_entry_t chain_cache[NUM_DRIVES][CHAIN_CACHE_SLOTS];

static void chain_cache_build(unsigned int slot) {
    uint32_t t0 = to_ms_since_boot(get_absolute_time());
    unsigned int cache_slot = 0;
    diskimage_entry_t e;

    for (unsigned int i = 0; i < CHAIN_CACHE_SLOTS; i++)
        chain_cache[slot][i].valid = false;

    for (unsigned int i = 0; diskimage_entry(&drives[slot].image, i, &e); i++) {
        if (e.file_type != DISKIMAGE_FTYPE_REL) continue;
        if (cache_slot >= CHAIN_CACHE_SLOTS) {
            log_info("ieee: drive %u: more REL files than %u cache slots",
                     slot, CHAIN_CACHE_SLOTS);
            break;
        }
        chain_cache_entry_t* c = &chain_cache[slot][cache_slot];
        if (!diskchain_build(&c->chain, &drives[slot].image,
                             e.start_track, e.start_sector))
            continue;
        c->track = e.start_track;
        c->sector = e.start_sector;
        c->valid = true;
        cache_slot++;
    }
    log_info("ieee: drive %u: %u REL chain(s) cached in %lu ms",
             slot, cache_slot,
             (unsigned long) (to_ms_since_boot(get_absolute_time()) - t0));
}

static const diskchain_t* chain_cache_find(unsigned int slot, uint8_t track,
                                           uint8_t sector) {
    for (unsigned int i = 0; i < CHAIN_CACHE_SLOTS; i++) {
        chain_cache_entry_t* c = &chain_cache[slot][i];
        if (c->valid && c->track == track && c->sector == sector) return &c->chain;
    }
    return NULL;
}

static bool file_read(void* ctx, uint32_t offset, void* buf, size_t len) {
    FILE* f = (FILE*) ctx;
    if (fseek(f, (long) offset, SEEK_SET) != 0) return false;
    return fread(buf, 1, len, f) == len;
}

static bool file_write(void* ctx, uint32_t offset, const void* buf, size_t len) {
    FILE* f = (FILE*) ctx;
    if (fseek(f, (long) offset, SEEK_SET) != 0) return false;
    if (fwrite(buf, 1, len, f) != len) return false;
    return fflush(f) == 0;      // persist promptly: power-off safety
}

// Mounts a path relative to /disks into a global drive slot.
static bool mount_image(unsigned int slot, const char* filename) {

    char path[SD_PATH_MAX];
    sd_make_path(path, SD_DIR_DISKS, filename);
    // Read-write when the card allows it (REL record writes, OS-9 format);
    // fall back to read-only rather than failing the mount.
    bool writable = true;
    FILE* f = fopen(path, "r+b");
    if (f == NULL) {
        writable = false;
        f = fopen(path, "rb");
    }
    if (f == NULL) return false;

    fseek(f, 0, SEEK_END);
    long size = ftell(f);

    // .hdd = flat hard-disk REL container (any 258-multiple size); everything
    // else opens by the exact d64/d80 container sizes.
    const char* dot = strrchr(filename, '.');
    bool is_hdd = (dot != NULL && strcasecmp(dot, ".hdd") == 0);

    diskimage_t img;
    bool opened = is_hdd ? diskimage_open_hdd(&img, file_read, f, (uint32_t) size)
                         : diskimage_open(&img, file_read, f, (uint32_t) size);
    if (!opened) {
        log_info("ieee: %s has unsupported size %ld, ignored", path, size);
        fclose(f);
        return false;
    }

    if (drives[slot].file != NULL) fclose(drives[slot].file);
    drives[slot].file = f;
    drives[slot].image = img;
    drives[slot].image.ctx = f;
    drives[slot].image.write = writable ? file_write : NULL;
    drives[slot].present = true;
    snprintf(drives[slot].name, sizeof(drives[slot].name), "%s", filename);
    log_info("ieee: drive %u = %s (%ld bytes)", slot, path, size);
    chain_cache_build(slot);
    return true;
}

// ----------------------------------------------------------------------------
// DOS state
// ----------------------------------------------------------------------------

typedef enum {
    st_code_ok = 0,
    st_code_read_error = 23,
    st_code_write_protect = 26,
    st_code_record_missing = 50,
    st_code_record_overflow = 51,
    st_code_file_not_found = 62,
    st_code_power_on = 73,
} status_code_t;

typedef struct {
    status_code_t code;
    uint8_t track;
    uint8_t sector;
    uint8_t drive;
} drive_status_t;

// Per-unit DOS status: each IEEE unit has its own channel-15 command channel,
// so status is tracked and served per unit.
static drive_status_t drive_status[NUM_UNITS] = {
    { .code = st_code_power_on },
    { .code = st_code_power_on },
    { .code = st_code_power_on },
    { .code = st_code_power_on },
};

static void set_status(unsigned int slot, status_code_t code, uint8_t track,
                       uint8_t sector) {
    drive_status[slot / DRIVES_PER_UNIT] = (drive_status_t) {
        .code = code,
        .track = track,
        .sector = sector,
        .drive = (uint8_t) (slot % DRIVES_PER_UNIT),
    };
}

static bool mcu_listening = false;  // mirrors the FPGA's addressed state
static bool mcu_talking = false;

// Which unit (0 = device 8 through 3 = device 11) the current LISTEN/TALK addressed.
// The secondary address that follows binds channels/status to that unit.
static uint8_t listen_unit = 0;
static uint8_t talk_unit = 0;
static uint8_t ch15_unit = 0;    // unit whose ch15 command is being collected
static uint8_t open_unit = 0;    // unit of the OPEN name being collected
static uint8_t file_unit = 0;    // unit of the open sequential file

static uint8_t stream_slot = 0;

static bool collecting_name = false;
static char open_name[48];
static unsigned int open_name_len = 0;
static uint8_t open_chan = 0;

// One data channel at a time (all the Waterloo loader needs).
static bool file_open_ok = false;
static uint8_t file_chan = 0;
static diskstream_t stream;
static bool streaming = false;      // TX top-up in progress
static bool stream_finished = false; // final byte (EOI) already queued
static uint32_t streamed_bytes = 0;

// ---------------------------------------------------------------------------
// CBM RELative-file channels (Super-OS/9 keeps its filesystems inside REL
// files, reclen 129, and reads them with ch15 'P' position commands).
// ---------------------------------------------------------------------------
#define MAX_REL_CHANNELS 4

typedef struct {
    bool in_use;
    uint8_t chan;           // secondary address 0-14 (unique per unit, not globally)
    uint8_t slot;           // global mount slot backing this channel
    uint8_t reclen;
    // Absolute byte offsets into the record stream (vdrive-rel.c semantics).
    // length = offset of the last non-zero byte; CBM DOS trims trailing
    // nulls and Super-OS/9 depends on that.
    uint32_t cur_record;    // 1-based, per CBM convention
    uint32_t bufptr;
    int32_t  length;
    bool     missing;       // positioned past the last record
    // Record-write staging (LISTEN data, committed at UNLISTEN):
    bool     wr_active;
    uint16_t wr_pos;        // start position within the record (from P)
    uint16_t wr_count;
    uint8_t  wr_buf[DISKIMAGE_REL_MAX_RECORD_LENGTH];
    diskchain_t chain;
} rel_channel_t;

static rel_channel_t rel_chans[MAX_REL_CHANNELS];

// Channels are keyed by (unit, chan): the d8d9 descriptor table reuses
// secondary addresses 2/3 on BOTH units, so the channel number alone is
// ambiguous.
static rel_channel_t* rel_find(uint8_t unit, uint8_t chan) {
    for (int i = 0; i < MAX_REL_CHANNELS; i++)
        if (rel_chans[i].in_use && rel_chans[i].chan == chan
            && rel_chans[i].slot / DRIVES_PER_UNIT == unit) return &rel_chans[i];
    return NULL;
}

// Channel-15 DOS command collection (LISTEN + secondary $6F, data, UNLISTEN)
static uint8_t ch15_cmd[40];
static unsigned int ch15_cmd_len = 0;
static bool collecting_ch15 = false;
static uint8_t listen_chan = 0xFF;  // active LISTEN data channel, $FF = none

// Resets DOS and protocol state that must not outlive initialization.
static void reset_protocol_state(void) {
    for (unsigned int unit = 0; unit < NUM_UNITS; unit++) {
        set_status(unit * DRIVES_PER_UNIT, st_code_power_on, 0, 0);
    }

    mcu_listening = false;
    mcu_talking = false;
    listen_unit = 0;
    talk_unit = 0;
    ch15_unit = 0;
    open_unit = 0;
    file_unit = 0;
    stream_slot = 0;
    collecting_name = false;
    open_name_len = 0;
    open_chan = 0;
    file_open_ok = false;
    file_chan = 0;
    stream = (diskstream_t) { 0 };
    streaming = false;
    stream_finished = false;
    streamed_bytes = 0;
    memset(rel_chans, 0, sizeof(rel_chans));
    memset(ch15_cmd, 0, sizeof(ch15_cmd));
    ch15_cmd_len = 0;
    collecting_ch15 = false;
    listen_chan = 0xFF;
}

static drive_model_t get_drive_model(unsigned int slot) {
    // First check for a disk present in the requested drive.  If that drive is
    // empty, try the other drive in the same unit.  If both drives are empty,
    // return the default drive model (4040).
    if (!drives[slot].present) slot ^= 1u;
    if (!drives[slot].present) return drive_model_4040;

    // Determine the drive model based on the type of the mounted disk image.
    const diskimage_type_t type = drives[slot].image.type;
    return type == diskimage_type_d80 || type == diskimage_type_hdd
        ? drive_model_8050
        : drive_model_4040;
}

// Position the engine at record 'rec', byte 'pos' within it, and compute
// the trimmed length (last non-zero byte), like vdrive_rel_position.
static void rel_position(rel_channel_t* rc, uint32_t rec, uint8_t pos) {
    uint8_t buf[DISKIMAGE_REL_MAX_RECORD_LENGTH];
    rc->cur_record = rec;
    rc->missing = (rec == 0)
        || rec > diskchain_size(&rc->chain) / rc->reclen;
    if (rc->missing) return;

    uint32_t base = (rec - 1) * (uint32_t) rc->reclen;
    rc->bufptr = base + pos;
    rc->length = (int32_t) (base + rc->reclen - 1);
    if (!diskchain_read(&rc->chain, base, buf, rc->reclen)) {
        rc->missing = true;
        return;
    }
    while (rc->length >= (int32_t) rc->bufptr
           && buf[rc->length - base] == 0) {
        rc->length--;
    }
}

// Serve the current (trimmed) record into the fabric TX FIFO, EOI on its
// last byte. Empty records are transparent: reads flow into the next
// record, exactly like vdrive_rel_read.
static void rel_serve(rel_channel_t* rc) {
    uint8_t buf[DISKIMAGE_REL_MAX_RECORD_LENGTH];

    ieee_ctrl_write(ECONOPET_IEEE_CTRL_ENABLE_MASK | ECONOPET_IEEE_CTRL_DATA_FLUSH_MASK);

    while (!rc->missing && (int32_t) rc->bufptr > rc->length) {
        rel_position(rc, rc->cur_record + 1, 0);
    }
    if (rc->missing) {
        set_status(rc->slot, st_code_record_missing, 0, 0);
        spi_write_at(ECONOPET_WB_IEEE_TX_LAST_ADDR, 0x0D);
        return;
    }

    uint16_t n = (uint16_t) (rc->length - rc->bufptr + 1);
    if (!diskchain_read(&rc->chain, rc->bufptr, buf, n)) {
        set_status(rc->slot, st_code_read_error, 0, 0);
        spi_write_at(ECONOPET_WB_IEEE_TX_LAST_ADDR, 0x0D);
        return;
    }
    // Burst, not per-byte: per-byte SPI can't outrun the CPU's drain. The
    // FIFO was just flushed and a record is <= 254 bytes, so it can't
    // overflow.
    if (n > 1) spi_write_same_block(ECONOPET_WB_IEEE_TX_ADDR, buf, n - 1u);
    spi_write_at(ECONOPET_WB_IEEE_TX_LAST_ADDR, buf[n - 1]);
    rc->bufptr += n;
    streamed_bytes += n;   // REL read, attributed to this channel's slot
}

// Begin collecting a record write on this channel (kernel did LISTEN +
// secondary): bytes land at the position set by the last P command.
static void rel_write_begin(rel_channel_t* rc) {
    uint32_t base = (rc->cur_record - 1) * (uint32_t) rc->reclen;
    rc->wr_active = true;
    rc->wr_count = 0;
    if (rc->missing || rc->bufptr < base || rc->bufptr >= base + rc->reclen) {
        rc->wr_pos = 0;         // fresh record start
    } else {
        rc->wr_pos = (uint16_t) (rc->bufptr - base);
    }
}

static void rel_write_byte(rel_channel_t* rc, uint8_t byte) {
    if (rc->wr_pos + rc->wr_count >= rc->reclen) {
        set_status(rc->slot, st_code_record_overflow, 0, 0);
        return;
    }
    rc->wr_buf[rc->wr_count++] = byte;
}

// Commit at UNLISTEN, CBM-style: bytes land at the position, the record
// tail is zero-filled (what the read side's null-trim recovers), and the
// engine advances.
static void rel_write_commit(rel_channel_t* rc) {
    uint8_t rec[DISKIMAGE_REL_MAX_RECORD_LENGTH];
    rc->wr_active = false;
    if (rc->missing) {
        set_status(rc->slot, st_code_record_missing, 0, 0);
        return;
    }
    uint32_t base = (rc->cur_record - 1) * (uint32_t) rc->reclen;
    if (!diskchain_read(&rc->chain, base, rec, rc->reclen)) {
        set_status(rc->slot, st_code_read_error, 0, 0);
        return;
    }
    memcpy(rec + rc->wr_pos, rc->wr_buf, rc->wr_count);
    memset(rec + rc->wr_pos + rc->wr_count, 0,
           rc->reclen - rc->wr_pos - rc->wr_count);
    if (!diskchain_write(&rc->chain, base, rec, rc->reclen)) {
        set_status(rc->slot, st_code_write_protect, 0, 0);
        log_info("ieee: REL write failed (read-only?) rec %lu",
                 (unsigned long) rc->cur_record);
        return;
    }
    rel_position(rc, rc->cur_record + 1, 0);     // advance like a real drive
}

// Execute a completed channel-15 command. Only 'P' (position) acts;
// 'I'/'V' succeed silently like a real drive.
static void ch15_execute(void) {
    if (ch15_cmd_len == 0) return;

    if (ch15_cmd[0] == 'P' && ch15_cmd_len >= 4) {
        // P + channel byte ($60 | chan) + record lo + record hi [+ position]
        rel_channel_t* rc = rel_find(ch15_unit, ch15_cmd[1] & 0x0F);
        uint32_t rec = ch15_cmd[2] | ((uint32_t) ch15_cmd[3] << 8);
        uint8_t pos = (ch15_cmd_len >= 5 && ch15_cmd[4] >= 1) ? (uint8_t) (ch15_cmd[4] - 1) : 0;
        if (rc == NULL) {
            set_status(ch15_unit * DRIVES_PER_UNIT
                       + drive_status[ch15_unit].drive,
                       st_code_file_not_found, 0, 0);
        } else {
            rel_position(rc, rec, pos);
            set_status(rc->slot,
                       rc->missing ? st_code_record_missing : st_code_ok, 0, 0);
        }
    } else if (ch15_cmd[0] == 'I' || ch15_cmd[0] == 'V') {
        uint8_t drive = drive_status[ch15_unit].drive;
        for (unsigned int index = 1; index < ch15_cmd_len; index++) {
            if (ch15_cmd[index] == '0' || ch15_cmd[index] == '1') {
                drive = (uint8_t) (ch15_cmd[index] - '0');
                break;
            }
        }
        set_status(ch15_unit * DRIVES_PER_UNIT + drive, st_code_ok, 0, 0);
    } else {
        log_info("ieee: ch15 command %02x len %u (ignored)", ch15_cmd[0], ch15_cmd_len);
    }
    ch15_cmd_len = 0;
}

static void resolve_open(void) {
    collecting_name = false;
    open_name[open_name_len] = '\0';

    // Split off the ",PRG"/",SEQ" type suffix.
    char* comma = strchr(open_name, ',');
    if (comma != NULL) *comma = '\0';

    // Channel 15 is the command channel: its "filename" is a DOS command
    // string, never a file open. Don't disturb the active data stream.
    if ((open_chan & 0x0F) == 0x0F) {
        log_info("ieee: DOS command '%s' (ignored)", open_name);
        return;
    }

    // Slot = the addressed unit's pair, plus the drive number from the
    // "0:"/"1:" (or "0."/"1.") prefix; default drive 0 of that unit.
    unsigned int slot = open_unit * DRIVES_PER_UNIT;
    if ((open_name[0] == '0' || open_name[0] == '1')
        && (open_name[1] == ':' || open_name[1] == '.')) {
        slot = open_unit * DRIVES_PER_UNIT
             + (unsigned int) (open_name[0] - '0');
    }
    // Fall back to the unit's other drive only for ordinary files: OS-9's
    // per-drive REL containers are drive-specific, and aliasing them can
    // corrupt the mounted system disk.
    bool is_os9_vol = (strstr(open_name, "OS9 DRIVE") != NULL)
                   || (strstr(open_name, "os9 drive") != NULL);
    if (!drives[slot].present && drives[slot ^ 1u].present && !is_os9_vol) {
        log_info("ieee: drive %u empty, using drive %u", slot, slot ^ 1u);
        slot ^= 1u;
    }

    file_open_ok = false;
    streaming = false;
    stream_finished = false;
    // New file: discard any stale queued data from a previous channel.
    ieee_ctrl_write(ECONOPET_IEEE_CTRL_ENABLE_MASK | ECONOPET_IEEE_CTRL_DATA_FLUSH_MASK);

    if (!drives[slot].present) {
        set_status(slot, st_code_file_not_found, 0, 0);
        log_info("ieee: OPEN '%s': no disk image mounted", open_name);
        return;
    }

    diskimage_entry_t entry;
    if (!diskimage_find(&drives[slot].image, open_name, &entry)) {
        set_status(slot, st_code_file_not_found, 0, 0);
        log_info("ieee: OPEN '%s': not found", open_name);
        return;
    }

    if (entry.file_type == DISKIMAGE_FTYPE_REL) {
        // Relative file: record-addressed access on this channel (used by
        // Super-OS/9 for its embedded filesystems). Reuse the slot if this
        // channel was already open, else take a free one.
        rel_channel_t* rc = rel_find(open_unit, open_chan & 0x0F);
        if (rc == NULL) {
            for (int i = 0; i < MAX_REL_CHANNELS; i++)
                if (!rel_chans[i].in_use) { rc = &rel_chans[i]; break; }
        }
        // Use the mount-time chain cache; live build only for chains it
        // doesn't know (e.g. more REL files than cache slots).
        const diskchain_t* cached = (rc != NULL)
            ? chain_cache_find(slot, entry.start_track, entry.start_sector)
            : NULL;
        if (cached != NULL) {
            rc->chain = *cached;
        }
        if (rc == NULL
            || (cached == NULL
                && !diskchain_build(&rc->chain, &drives[slot].image,
                                    entry.start_track, entry.start_sector))) {
            set_status(slot, st_code_file_not_found, 0, 0);
            log_info("ieee: REL OPEN '%s' failed", open_name);
            return;
        }
        if (entry.record_len > DISKIMAGE_REL_MAX_RECORD_LENGTH) {
            set_status(slot, st_code_file_not_found, 0, 0);
            log_info("ieee: REL OPEN '%s' bad reclen %u", open_name, entry.record_len);
            return;
        }
        rc->in_use = true;
        rc->slot = (uint8_t) slot;
        rc->chan = open_chan & 0x0F;
        rc->reclen = entry.record_len >= DISKIMAGE_REL_MIN_RECORD_LENGTH
            ? entry.record_len : 129;
        rel_position(rc, 1, 0);
        set_status(slot, st_code_ok, 0, 0);
        log_info("ieee: REL OPEN '%s' ok (chan %u, reclen %u, %lu bytes)",
                 open_name, rc->chan, rc->reclen,
                 (unsigned long) diskchain_size(&rc->chain));
        return;
    }

    if (!diskstream_open(&stream, &drives[slot].image,
                         entry.start_track, entry.start_sector)) {
        set_status(slot, st_code_file_not_found, 0, 0);
        log_info("ieee: OPEN '%s': stream open failed", open_name);
        return;
    }

    file_open_ok = true;
    stream_slot = (uint8_t) slot;
    stream_finished = false;
    file_chan = open_chan;
    file_unit = open_unit;
    set_status(slot, st_code_ok, 0, 0);
    streamed_bytes = 0;
    log_info("ieee: OPEN '%s' ok (chan %u)", open_name, file_chan);
}

static void push_status(unsigned int unit) {
    const char* text;
    char line[IEEE_STATUS_LINE_CAPACITY];
    const drive_status_t status = drive_status[unit];
    const drive_model_t model =
        get_drive_model(unit * DRIVES_PER_UNIT + status.drive);

    switch (status.code) {
        case st_code_ok:              text = " OK"; break;
        case st_code_read_error:      text = "READ ERROR"; break;
        case st_code_write_protect:   text = "WRITE PROTECT ON"; break;
        case st_code_record_missing:  text = "RECORD NOT PRESENT"; break;
        case st_code_record_overflow: text = "OVERFLOW IN RECORD"; break;
        case st_code_file_not_found:  text = "FILE NOT FOUND"; break;
        case st_code_power_on:
            text = model == drive_model_8050
                ? "CBM DOS V2.7"
                : "CBM DOS V2";
            break;
        default:                      text = ""; break;
    }
    const int n = model == drive_model_8050
        ? snprintf(line, sizeof(line), "%02u,%s,%02u,%02u,%u",
                   (unsigned int) status.code, text, status.track, status.sector,
                   status.drive)
        : snprintf(line, sizeof(line), "%02u,%s,%02u,%02u",
                   (unsigned int) status.code, text, status.track, status.sector);

    vet(n >= 0 && (size_t) n <= IEEE_STATUS_TEXT_MAX,
        "IEEE status text exceeds its %u-byte capacity", IEEE_STATUS_TEXT_MAX);
    for (int i = 0; i < n; i++) spi_write_at(ECONOPET_WB_IEEE_TXS_ADDR, (uint8_t) line[i]);
    spi_write_at(ECONOPET_WB_IEEE_TXS_LAST_ADDR, 0x0D);

    // Reading the status channel resets it, like a real drive.
    drive_status[unit].code = st_code_ok;
    drive_status[unit].track = 0;
    drive_status[unit].sector = 0;
}

// Fill the TX FIFO from the open stream until the fabric reports no room
// for another chunk.
static void service_tx(void) {
    // An underrun mid-record times out the kernel's counted read.
    uint8_t buf[ECONOPET_IEEE_TX_BURST_CHUNK];

    for (;;) {
        uint8_t ctrl = spi_read_at(ECONOPET_WB_IEEE_CTRL_ADDR);
        if (!(ctrl & ECONOPET_IEEE_CTRL_RD_TX_ROOM_MASK)) return;

        size_t n = 0;
        bool last = false;
        uint8_t last_byte = 0;

        while (n < ECONOPET_IEEE_TX_BURST_CHUNK) {
            uint8_t byte;
            bool is_last;
            if (!diskstream_next(&stream, &byte, &is_last)) {
                // Natural EOF exits via 'is_last'; reaching here mid-file means
                // an SD read error. Flush what we gathered, then close with an
                // EOI'd filler so the kernel sees a clean (if short) end.
                if (n > 0) spi_write_same_block(ECONOPET_WB_IEEE_TX_ADDR, buf, n);
                streamed_bytes += n;
                log_info("ieee: read error after %lu bytes", (unsigned long) streamed_bytes);
                set_status(stream_slot, st_code_read_error, 0, 0);
                spi_write_at(ECONOPET_WB_IEEE_TX_LAST_ADDR, 0x0D);
                streaming = false;
                return;
            }
            if (is_last) { last = true; last_byte = byte; break; }
            buf[n++] = byte;
        }

        if (n > 0) spi_write_same_block(ECONOPET_WB_IEEE_TX_ADDR, buf, n);
        streamed_bytes += n;

        if (last) {
            // Final byte carries EOI: separate address, so not part of the burst.
            spi_write_at(ECONOPET_WB_IEEE_TX_LAST_ADDR, last_byte);
            streamed_bytes++;
            log_info("ieee: stream complete, %lu bytes", (unsigned long) streamed_bytes);
            streaming = false;
            stream_finished = true;
            return;
        }
    }
}

static void handle_command(uint8_t cmd) {
    switch (IEEE_CMD_CLASS(cmd)) {
        case IEEE_CMD_LISTEN_BASE:  // LISTEN / UNLISTEN
            if (cmd == IEEE_CMD_UNLISTEN) {
                if (collecting_name) resolve_open();
                if (collecting_ch15) { collecting_ch15 = false; ch15_execute(); }
                for (int i = 0; i < MAX_REL_CHANNELS; i++)
                    if (rel_chans[i].in_use && rel_chans[i].wr_active)
                        rel_write_commit(&rel_chans[i]);
                mcu_listening = false;
                listen_chan = 0xFF;
            } else {
                uint8_t a = IEEE_CMD_ADDRESS(cmd);
                mcu_listening = (a >= DEV_ADDR && a < DEV_ADDR + NUM_UNITS);
                if (mcu_listening) listen_unit = (uint8_t) (a - DEV_ADDR);
            }
            break;

        case IEEE_CMD_TALK_BASE:  // TALK / UNTALK
            if (cmd == IEEE_CMD_UNTALK) {
                mcu_talking = false;
                // Channel data persists across UNTALK (continuation) -- just
                // pause the top-up until the next TALK on the data channel.
                streaming = false;
            } else {
                uint8_t a = IEEE_CMD_ADDRESS(cmd);
                mcu_talking = (a >= DEV_ADDR && a < DEV_ADDR + NUM_UNITS);
                if (mcu_talking) talk_unit = (uint8_t) (a - DEV_ADDR);
            }
            break;

        case IEEE_CMD_SECONDARY_BASE:  // secondary address (data channel)
            if (mcu_listening) {
                rel_channel_t* wrc;
                listen_chan = IEEE_CMD_CHANNEL(cmd);
                if (listen_chan == 15) {
                    collecting_ch15 = true;
                    ch15_unit = listen_unit;
                    ch15_cmd_len = 0;
                } else if ((wrc = rel_find(listen_unit, listen_chan)) != NULL) {
                    rel_write_begin(wrc);
                }
            }
            if (mcu_talking) {
                uint8_t chan = IEEE_CMD_CHANNEL(cmd);
                rel_channel_t* rc;
                if (chan == 15) {
                    push_status(talk_unit);
                } else if ((rc = rel_find(talk_unit, chan)) != NULL) {
                    rel_serve(rc);
                } else if (file_open_ok && talk_unit == file_unit && chan == file_chan) {
                    if (stream_finished) {
                        // Read past EOF: real CBM DOS answers a lone EOI'd
                        // CR with clean status, not a read error.
                        spi_write_at(ECONOPET_WB_IEEE_TX_LAST_ADDR, 0x0D);
                    } else {
                        streaming = true;
                    }
                }
            }
            break;

        case IEEE_CMD_CLOSE_BASE:  // CLOSE ($Ex) / OPEN ($Fx)
            if (IEEE_CMD_IS_OPEN(cmd)) {
                if (mcu_listening) {
                    open_chan = IEEE_CMD_CHANNEL(cmd);
                    open_unit = listen_unit;
                    collecting_name = true;
                    open_name_len = 0;
                }
            } else {
                if (mcu_listening) {
                    rel_channel_t* rc = rel_find(listen_unit, IEEE_CMD_CHANNEL(cmd));
                    if (rc != NULL) {
                        rc->in_use = false;
                        ieee_ctrl_write(ECONOPET_IEEE_CTRL_ENABLE_MASK | ECONOPET_IEEE_CTRL_DATA_FLUSH_MASK);
                    } else if (listen_unit == file_unit && IEEE_CMD_CHANNEL(cmd) == file_chan) {
                        file_open_ok = false;
                        streaming = false;
                        stream_finished = false;
                        ieee_ctrl_write(ECONOPET_IEEE_CTRL_ENABLE_MASK | ECONOPET_IEEE_CTRL_DATA_FLUSH_MASK);
                    }
                }
            }
            break;

        default:
            break;
    }
}

// ----------------------------------------------------------------------------
// Public API
// ----------------------------------------------------------------------------

static void sync_emulation_enabled(void) {
    bool has_mounted_drive = false;
    for (unsigned int slot = 0; slot < NUM_DRIVES; slot++) {
        if (drives[slot].present) {
            has_mounted_drive = true;
            break;
        }
    }
    emulation_enabled = has_mounted_drive;
    if (emulation_enabled) {
        ieee_ctrl_write(ECONOPET_IEEE_CTRL_ENABLE_MASK | ECONOPET_IEEE_CTRL_FLUSH_MASK);
        log_info("ieee: virtual drive enabled");
    } else {
        ieee_ctrl_write(0);
        log_info("ieee: virtual drive off (real hardware bus)");
    }
}

void ieee_drive_init(void) {
    // Initialization always starts from a stock-PET bus and fresh DOS state.
    ieee_drive_unmount_all();
}

void ieee_drive_reset(void) {
    reset_protocol_state();
    if (emulation_enabled) ieee_ctrl_write(ECONOPET_IEEE_CTRL_ENABLE_MASK | ECONOPET_IEEE_CTRL_FLUSH_MASK);
}

void ieee_drive_unmount_all(void) {
    for (unsigned int slot = 0; slot < NUM_DRIVES; slot++) {
        if (drives[slot].file != NULL) fclose(drives[slot].file);
        drives[slot] = (drive_t) { 0 };
        for (unsigned int i = 0; i < CHAIN_CACHE_SLOTS; i++) {
            chain_cache[slot][i].valid = false;
        }
    }
    reset_protocol_state();
    sync_emulation_enabled();
}

bool ieee_drive_mount(unsigned int slot, const char* filename) {
    if (slot >= NUM_DRIVES) return false;

    bool mounted = mount_image(slot, filename);
    if (!mounted) log_info("ieee: could not mount disk image: /disks/%s", filename);
    if (mounted) sync_emulation_enabled();
    return mounted;
}

void ieee_drive_task(void) {
    if (!emulation_enabled) return;

    // Drain the RX FIFO (commands and listener data).
    for (unsigned int i = 0; i < 64; i++) {
        uint8_t st = spi_read_at(ECONOPET_WB_IEEE_STATUS_ADDR);
        if (!(st & ECONOPET_IEEE_ST_RX_AVAIL_MASK)) break;

        bool is_atn = (st & ECONOPET_IEEE_ST_RX_ATN_MASK) != 0;
        uint8_t byte = spi_read_at(ECONOPET_WB_IEEE_RX_ADDR);
        spi_write_at(ECONOPET_WB_IEEE_RX_ADDR, 0);   // explicit pop (reads are side-effect-free)

        if (is_atn) {
            handle_command(byte);
        } else {
            if (collecting_name && open_name_len < sizeof(open_name) - 1) {
                open_name[open_name_len++] = (char) byte;
            } else if (collecting_ch15 && ch15_cmd_len < sizeof(ch15_cmd)) {
                ch15_cmd[ch15_cmd_len++] = byte;
            } else if (listen_chan != 0xFF) {
                rel_channel_t* wrc = rel_find(listen_unit, listen_chan);
                if (wrc != NULL && wrc->wr_active) {
                    rel_write_byte(wrc, byte);   // REL write on this channel's slot
                }
            }
        }
    }

    if (streaming) service_tx();
}
