DLehenbauer/econopet/fw/src/system_state.c

// SPDX-License-Identifier: CC0-1.0
// https://github.com/dlehenbauer/econopet

#include "pch.h"
#include "system_state.h"

system_state_t system_state = {
    .pet_keyboard_model = pet_keyboard_model_graphics,
    .pet_video_type = pet_video_type_fixed,
    .pet_display_columns = pet_display_columns_40,
    .video_ram_mask = pet_video_ram_mask_1kb,
    .video_ram_bytes = 1024,    // 1KB    
    .video_source = video_source_firmware,
    .term_mode = term_mode_cli,
    .video_text_mode = video_text_mode_graphics,
    .pet_crtc_registers = {
        [CRTC_R0_H_TOTAL]        = 0x31, // Horizontal total (minus one)
        [CRTC_R1_H_DISPLAYED]    = 0x28, // Displayed (40 chars)
        [CRTC_R2_H_SYNC_POS]     = 0x29, // HSYNC position
        [CRTC_R3_SYNC_WIDTH]     = 0x0F, // Sync widths
        [CRTC_R4_V_TOTAL]        = 0x28, // Vertical total (minus one)
        [CRTC_R5_V_ADJUST]       = 0x05, // Vertical adjust
        [CRTC_R6_V_DISPLAYED]    = 0x19, // Vertical displayed (25 rows)
        [CRTC_R7_V_SYNC_POS]     = 0x21, // VSYNC position
        [CRTC_R8_MODE_CONTROL]   = 0x00, // Mode control (unused)
        [CRTC_R9_MAX_SCAN_LINE]  = 0x07, // Num scan lines per row (minus one)
        [CRTC_R12_START_ADDR_HI] = 0x10, // Display start high (ma[13]=0: no option ROM, ma[12]=1: normal video)
        [CRTC_R13_START_ADDR_LO] = 0x00, // Display start low
    }
};

void system_state_set_video_ram_mask(system_state_t* state, uint8_t video_ram_mask) {
    state->video_ram_mask = video_ram_mask;
    state->video_ram_bytes = (size_t)(video_ram_mask + 1) * 1024u;
}
