DLehenbauer/econopet/gw/EconoPET/src/ram.sv

// SPDX-License-Identifier: CC0-1.0
// https://github.com/dlehenbauer/econopet

`timescale 1ns / 1ps

import common_pkg::*;

// Wishbone peripheral that allows the MCU to access RAM (via SPI bridge).
// The arbiter grants this peripheral control of the system bus between
// video and CPU accesses.
module ram (
    // Wishbone B4 peripheral
    // (See https://cdn.opencores.org/downloads/wbspec_b4.pdf)
    input  logic wb_clock_i,
    input  logic [WB_ADDR_WIDTH-1:0] wbp_addr_i,
    input  logic [   DATA_WIDTH-1:0] wbp_data_i,     // Incoming data to write to RAM
    output logic [   DATA_WIDTH-1:0] wbp_data_o,     // Outgoing data read from RAM
    input  logic wbp_we_i,                           // Direction of transaction (0 = read , 1 = write)
    input  logic wbp_cycle_i,                        // Bus cycle is active
    input  logic wbp_strobe_i,                       // New transaction requested (address, data, and control signals are valid)
    output logic wbp_stall_o,                        // Peripheral is not ready to accept the request
    output logic wbp_ack_o,                          // Indicates success termination of cycle (data_o is valid)
    input  logic wbp_sel_i,                          // Asserted when selected by 'wbp_addr_i'

    // RAM interface
    output logic                      ram_oe_o,     // OE asserted for reads from RAM
    output logic                      ram_we_o,     // WE asserted for writes to RAM
    output logic [RAM_ADDR_WIDTH-1:0] ram_addr_o,   // RAM address bus
    input  logic [    DATA_WIDTH-1:0] ram_data_i,   // Incoming data from RAM during reads
    output logic [    DATA_WIDTH-1:0] ram_data_o,   // Outgoing data to RAM during writes
    output logic                      ram_data_oe   // Tri-state enable for FPGA data driver (asserted during writes)
);
    // Timing for AS6C1008-55PCN
    // (See: https://www.alliancememory.com/wp-content/uploads/AS6C1008_Mar_2023V1.2.pdf)
    //
    // Read cycle
    //
    // | Symbol | Parameter                                | Min | Max | Units |
    // |--------|------------------------------------------|-----|-----|-------|
    // | tRC    | Read Cycle Time                          |  55 |   - | ns    |
    // | tAA    | Address Access Time                      |   - |  55 | ns    |
    // | tACE   | Chip Enable Access Time                  |   - |  55 | ns    |
    // | tOE    | Output Enable Access Time                |   - |  30 | ns    |
    // | tCLZ   | Chip Enable to Output in Low-Z           |   - |  10 | ns    |
    // | tOLZ   | Output Enable to Output in Low-Z         |   - |   5 | ns    |
    // | tCHZ   | Chip Disable to Output in High-Z         |   - |  20 | ns    |
    // | tOHZ   | Output Disable to Output in High-Z       |   - |  20 | ns    |
    // | tOH    | Output Hold from Address Change          |  10 |   - | ns    |
    //
    // Summary:
    //
    // - DOUT valid 55ns after coincident ADDR and OE: max(tAA, tOE, tOLZ).
    // - DOUT held 10ns after ADDR changes.
    // - DOUT returns to High-Z 20ns after OE deasserted.
    // - CE is permenantly asserted, so tACE, tCLZ, tCHZ, and tCW are not relevant.
    //
    //              |<-- 55ns -->|     |<-- 20ns ->|
    //              |            |     |           |
    // ADDR  -------<_̅_̅_̅_̅_̅_̅_̅_̅_̅_̅_̅_̅_̅_̅_̅_̅_̅_>----------------
    //                           |     |           |
    //   OE  _______/‾‾‾‾‾‾‾‾‾‾‾‾‾‾‾‾‾‾\________________
    //                           |     |           |
    // DOUT  -------------------<̅_̅_̅_̅_̅_̅_X_̅_̅_̅_̅_X_̅_̅_̅_̅_>----
    //
    // Write cycle
    //
    // | Symbol | Parameter                                | Min | Max | Units |
    // |--------|------------------------------------------|-----|-----|-------|
    // | tWC    | Write Cycle Time                         |  55 |   - | ns    |
    // | tAW    | Address Valid to End of Write            |  50 |   - | ns    |
    // | tAS    | Address Setup Time                       |   0 |   - | ns    |
    // | tWP    | Write Pulse Width                        |  45 |   - | ns    |
    // | tWR    | Write Recovery Time                      |   0 |   - | ns    |
    // | tDW    | Data to Write Time Overlap               |  25 |   - | ns    |
    // | tDH    | Data Hold from End of Write Time         |   0 |   - | ns    |
    // | tOW    | Output Active from End of Write          |   5 |   - | ns    |
    // | tWHZ   | Write to Output in High-Z                |   - |  20 | ns    |
    //
    // Summary:
    // 
    // - Total write cycle time must be at least 55ns (tWC).
    // - ADDR must be valid 50ns before WE deasserts; no hold requirement (tAW, tWR = 0ns).
    // - DIN must be valid 25ns before WE deasserts; no hold requirement (tDW, tDH = 0ns).
    // - WE pulse width must be at least 45ns (tWP).
    // - OE is deasserted during writes, so tOW and tWHZ are not relevant.
    //
    //           |<---- 50ns --->|
    //           |  |<-- 45ns -->|
    //           |  |            |
    // ADDR  ----<̅_̅_̅_̅_̅_̅_̅_̅_̅_̅_̅_̅_̅_̅_̅_>-----
    //                           |
    //   WE  _______/‾‾‾‾‾‾‾‾‾‾‾‾\_____
    //                           |
    //  DIN  ---------------<̅_̅_̅_̅_>-----
    //                      |    |
    //                      |25ns|

    localparam READ_HOLD_COUNT  = common_pkg::ns_to_cycles(SRAM_tAA);
    localparam WRITE_HOLD_COUNT = common_pkg::ns_to_cycles(SRAM_tWP);

    localparam bit [3:0] READY   = 4'b0001,
                         READING = 4'b0010,
                         HIGHZ   = 4'b0100,
                         WRITING = 4'b1000;

    logic [3:0] state = READY;
    logic [2:0] cycle_count = '0;

    // FPGA drives system data bus when Wishbone peripheral is writing to RAM
    assign ram_data_oe = ram_we_o;

    initial begin
        wbp_ack_o   = '0;
        wbp_stall_o = '0;
        ram_oe_o    = '0;
        ram_we_o    = '0;
    end

    always_ff @(posedge wb_clock_i) begin
        unique case (state)
            READY: begin
                wbp_ack_o   <= '0;
                wbp_stall_o <= '0;
                ram_oe_o    <= '0;
                ram_we_o    <= '0;
                cycle_count <= '0;

                if (wbp_sel_i && wbp_cycle_i && wbp_strobe_i) begin
                    ram_addr_o  <= wbp_addr_i[RAM_ADDR_WIDTH-1:0];
                    ram_data_o  <= wbp_data_i;
                    wbp_stall_o <= 1'b1;
                    ram_oe_o    <= !wbp_we_i;
                    ram_we_o    <=  wbp_we_i;
                    state <= wbp_we_i
                        ? WRITING
                        : READING;
                end
            end
            READING: begin
                if (cycle_count == $bits(cycle_count)'(READ_HOLD_COUNT)) begin
                    cycle_count <= '0;
                    wbp_data_o <= ram_data_i;
                    wbp_ack_o <= 1'b1;
                    ram_oe_o <= '0;
                    state <= HIGHZ;
                end else cycle_count <= cycle_count + 1'b1;
            end
            HIGHZ: begin
                wbp_ack_o <= '0;
                wbp_stall_o <= '0;
                state <= READY;
            end
            WRITING: begin
                if (cycle_count == $bits(cycle_count)'(WRITE_HOLD_COUNT)) begin
                    wbp_ack_o   <= 1'b1;
                    wbp_stall_o <= '0;
                    ram_we_o    <= '0;
                    state <= READY;
                end else cycle_count <= cycle_count + 1'b1;
            end
            default: begin
                // synthesis off
                $fatal(1, "Illegal 'state' value: %0d", state);
                // synthesis on
            end
        endcase
    end

    // synthesis off

    // OE is asserted in READY and deasserted in READING when cycle_count
    // matches, giving (READ_HOLD_COUNT + 1) cycles of OE.  The HIGHZ state
    // adds one cycle before READY, so the total read cycle (address valid to
    // next possible address change) is (READ_HOLD_COUNT + 3) cycles.
    localparam int READ_OE_CYCLES    = READ_HOLD_COUNT + 1;
    localparam int READ_TOTAL_CYCLES = READ_HOLD_COUNT + 3;

    // WE is asserted in READY and deasserted in WRITING when cycle_count
    // matches, giving (WRITE_HOLD_COUNT + 1) cycles of WE.  WRITING returns
    // directly to READY, so the total write cycle is (WRITE_HOLD_COUNT + 2).
    localparam int WRITE_WE_CYCLES    = WRITE_HOLD_COUNT + 1;
    localparam int WRITE_TOTAL_CYCLES = WRITE_HOLD_COUNT + 2;

    initial begin
        // Hold counts must fit in cycle_count width
        if (READ_HOLD_COUNT > 2**$bits(cycle_count) - 1)
            $fatal(1, "READ_HOLD_COUNT (%0d) exceeds cycle_count max (%0d)",
                READ_HOLD_COUNT, 2**$bits(cycle_count) - 1);
        if (WRITE_HOLD_COUNT > 2**$bits(cycle_count) - 1)
            $fatal(1, "WRITE_HOLD_COUNT (%0d) exceeds cycle_count max (%0d)",
                WRITE_HOLD_COUNT, 2**$bits(cycle_count) - 1);

        // Read: OE pulse must allow address access time plus round-trip
        // trace delay (address out to SRAM, data back to FPGA)
        if (READ_OE_CYCLES * NS_PER_CYCLE < SRAM_tAA + 2 * MAX_TRACE_DELAY_NS)
            $fatal(1, "Read OE pulse %.1fns violates tAA + 2*trace >= %0dns",
                READ_OE_CYCLES * NS_PER_CYCLE, SRAM_tAA + 2 * MAX_TRACE_DELAY_NS);

        // Read: OE pulse must allow output enable access time plus
        // round-trip trace delay
        if (READ_OE_CYCLES * NS_PER_CYCLE < SRAM_tOE + 2 * MAX_TRACE_DELAY_NS)
            $fatal(1, "Read OE pulse %.1fns violates tOE + 2*trace >= %0dns",
                READ_OE_CYCLES * NS_PER_CYCLE, SRAM_tOE + 2 * MAX_TRACE_DELAY_NS);

        // Read: total cycle must meet minimum read cycle time
        if (READ_TOTAL_CYCLES * NS_PER_CYCLE < SRAM_tRC)
            $fatal(1, "Read cycle %.1fns violates tRC >= %0dns",
                READ_TOTAL_CYCLES * NS_PER_CYCLE, SRAM_tRC);

        // Write: WE pulse must meet minimum pulse width
        if (WRITE_WE_CYCLES * NS_PER_CYCLE < SRAM_tWP)
            $fatal(1, "Write WE pulse %.1fns violates tWP >= %0dns",
                WRITE_WE_CYCLES * NS_PER_CYCLE, SRAM_tWP);

        // Write: address must be valid at least tAW before WE deasserts
        if (WRITE_WE_CYCLES * NS_PER_CYCLE < SRAM_tAW)
            $fatal(1, "Write address setup %.1fns violates tAW >= %0dns",
                WRITE_WE_CYCLES * NS_PER_CYCLE, SRAM_tAW);

        // Write: data must be valid at least tDW before WE deasserts
        if (WRITE_WE_CYCLES * NS_PER_CYCLE < SRAM_tDW)
            $fatal(1, "Write data setup %.1fns violates tDW >= %0dns",
                WRITE_WE_CYCLES * NS_PER_CYCLE, SRAM_tDW);

        // Write: total cycle must meet minimum write cycle time
        if (WRITE_TOTAL_CYCLES * NS_PER_CYCLE < SRAM_tWC)
            $fatal(1, "Write cycle %.1fns violates tWC >= %0dns",
                WRITE_TOTAL_CYCLES * NS_PER_CYCLE, SRAM_tWC);
    end
    // synthesis on
endmodule
