DLehenbauer/econopet/fw/src/menu/menu.h

// SPDX-License-Identifier: CC0-1.0
// https://github.com/dlehenbauer/econopet

#pragma once

#include "system_state.h"

void menu_enter(bool is_boot);
void menu_task(void);
void read_keymap(const char* filename, system_state_t* config);
