DLehenbauer/econopet/gw/EconoPET/src/register_file.sv

// SPDX-License-Identifier: CC0-1.0
// https://github.com/dlehenbauer/econopet

import common_pkg::*;

module register_file(
    // Wishbone B4 peripheral
    // (See https://cdn.opencores.org/downloads/wbspec_b4.pdf)
    input  logic                      wb_clock_i,
    input  logic [WB_ADDR_WIDTH-1:0]  wbp_addr_i,
    input  logic [   DATA_WIDTH-1:0]  wbp_data_i,
    output logic [   DATA_WIDTH-1:0]  wbp_data_o,
    input  logic                      wbp_we_i,
    input  logic                      wbp_cycle_i,
    input  logic                      wbp_strobe_i,
    output logic                      wbp_stall_o,
    output logic                      wbp_ack_o,
    input  logic                      wbp_sel_i,         // Asserted when selected by 'wbp_addr_i'

    // Status register
    input  logic                      text_mode_i,       // VIA CA2 (0 = upper/graphics, 1 = upper/lower)
    input  logic                      config_crt_i,      // Display type (0 = 12"/CRTC/20kHz, 1 = 9"/non-CRTC/15kHz)
    input  logic                      config_keyboard_i, // Keyboard type (0 = Business, 1 = Graphics)
    input  logic                      phys_cpu_active_i, // Physical 6502 address activity detected

    // CPU register
    output logic                      cpu_ready_o,
    output logic                      cpu_reset_o,
    output logic                      cpu_nmi_o,
    output logic [1:0]                cpu_sel_o,         // CPU_SEL_* (phys 6502 / soft 6809 / soft 6502)
    output logic                      superpet_io_o,     // machine type: SuperPET I/O visible to a 6502 too
    output logic                      cpu_sel_wr_o,      // 1-cycle pulse when REG_CPU_SEL is written (arms/clears the detector)

    // Breakpoint
    input  logic                      bp_halted_i,       // Breakpoint module has halted the CPU
    input  logic [CPU_ADDR_WIDTH-1:0] bp_addr_i,         // CPU address where breakpoint was hit
    output logic                      bp_clear_o,        // One-cycle pulse to clear breakpoint halt

    // Video register
    output logic                      video_col_80_mode_o,
    output logic [11:10]              video_ram_mask_o
);
    logic [DATA_WIDTH-1:0] register[REG_COUNT-1:0];

    initial begin
        wbp_ack_o    = '0;
        bp_clear_o   = '0;
        cpu_sel_wr_o = '0;

        register[REG_STATUS] = '0;

        // CPU state at power on:
        register[REG_CPU][REG_CPU_READY_BIT] = 1'b0;    // Not ready
        register[REG_CPU][REG_CPU_RESET_BIT] = 1'b1;    // Reset
        register[REG_CPU][REG_CPU_NMI_BIT]   = 1'b0;    // Not NMI

        // CPU select at power on: the physical 6502, matching a stock
        // board. Firmware selects soft cores explicitly (menu and configs).
        register[REG_CPU_SEL][1:0] = CPU_SEL_PHYS_6502;
        register[REG_CPU_SEL][CPU_SEL_SUPERPET_IO_BIT] = 1'b0;

        // Video state at power on: 40 column mode, 1KB video RAM
        register[REG_VIDEO][REG_VIDEO_COL_80_BIT]        = 1'b0;
        register[REG_VIDEO][REG_VIDEO_RAM_MASK_HI_BIT]   = 1'b0;
        register[REG_VIDEO][REG_VIDEO_RAM_MASK_LO_BIT]   = 1'b0;

        // Breakpoint registers at power on:
        register[REG_BP_CTL]     = '0;
        register[REG_BP_ADDR_HI] = '0;
    end

    // This peripheral always completes WB operations in a single cycle.
    assign wbp_stall_o = 1'b0;

    wire [REG_ADDR_WIDTH-1:0] reg_addr = wbp_addr_i[REG_ADDR_WIDTH-1:0];

    always_ff @(posedge wb_clock_i) begin
        bp_clear_o   <= '0;
        cpu_sel_wr_o <= '0;

        if (wbp_sel_i && wbp_cycle_i && wbp_strobe_i) begin
            wbp_data_o <= register[reg_addr];
            if (wbp_we_i) begin
                // Writing to REG_BP_CTL pulses bp_clear_o instead of storing
                // the value (the register address is shared with REG_BP_ADDR_LO
                // which is read-only).
                if (reg_addr == REG_STATUS[REG_ADDR_WIDTH-1:0]) begin
                    // REG_STATUS is read-only.
                end else if (reg_addr == REG_BP_CTL[REG_ADDR_WIDTH-1:0]) begin
                    bp_clear_o <= wbp_data_i[REG_BP_CTL_CLEAR_BIT];
                end else begin
                    register[reg_addr] <= wbp_data_i;
                    // Writing the CPU-select register arms/clears the physical-
                    // CPU activity detector (see main.sv).
                    if (reg_addr == REG_CPU_SEL[REG_ADDR_WIDTH-1:0]) begin
                        cpu_sel_wr_o <= 1'b1;
                    end
                end
            end
            wbp_ack_o <= 1'b1;
        end else begin
            wbp_ack_o <= '0;

            // Refresh status registers while not in a wishbone cycle.  This happens at
            // 64 MHz, which is guaranteed to restore overwritten status bits before
            // we process the next SPI command.
            //
            // Order must match bit order declared in common_pkg.sv.
            register[REG_STATUS] <= { 3'b000, phys_cpu_active_i,
                                      bp_halted_i, config_keyboard_i, config_crt_i,
                                      text_mode_i};

            // Refresh breakpoint address registers from the breakpoint module.
            register[REG_BP_ADDR_LO] <= bp_addr_i[7:0];
            register[REG_BP_ADDR_HI] <= bp_addr_i[15:8];
        end
    end

    assign cpu_ready_o         = register[REG_CPU][REG_CPU_READY_BIT];
    assign cpu_reset_o         = register[REG_CPU][REG_CPU_RESET_BIT];
    assign cpu_nmi_o           = register[REG_CPU][REG_CPU_NMI_BIT];
    assign cpu_sel_o           = register[REG_CPU_SEL][1:0];
    assign superpet_io_o = register[REG_CPU_SEL][CPU_SEL_SUPERPET_IO_BIT];
    
    assign video_col_80_mode_o = register[REG_VIDEO][REG_VIDEO_COL_80_BIT];
    assign video_ram_mask_o    = register[REG_VIDEO][REG_VIDEO_RAM_MASK_HI_BIT:REG_VIDEO_RAM_MASK_LO_BIT];
endmodule
