DLehenbauer/econopet/gw/EconoPET/src/video_crtc_reg.sv

// SPDX-License-Identifier: CC0-1.0
// https://github.com/dlehenbauer/econopet

import common_pkg::*;

module video_crtc_reg (
    // Wishbone B4 peripheral to read/write current CRTC register values.
    // (See: https://cdn.opencores.org/downloads/wbspec_b4.pdf)
    input  logic wb_clock_i,                     // FPGA System clock
    input  logic [WB_ADDR_WIDTH-1:0] wbp_addr_i, // Address of pending read/write (valid when 'cycle_o' asserted)
    input  logic [   DATA_WIDTH-1:0] wbp_data_i, // Data received from MCU to write (valid when 'cycle_o' asserted)
    output logic [   DATA_WIDTH-1:0] wbp_data_o, // Data to transmit to MCU (valid when 'ack_o' asserted)
    input  logic wbp_we_i,                       // Direction of transaction (0 = read , 1 = write)
    input  logic wbp_cycle_i,                    // Bus cycle is active
    input  logic wbp_strobe_i,                   // New transaction requested (address, data, and control signals are valid)
    output logic wbp_stall_o,                    // Peripheral is not ready to accept the request
    output logic wbp_ack_o,                      // Indicates success termination of cycle (data_o is valid)
    input  logic wbp_sel_i,                      // Asserted when selected by 'wbp_addr_i'
    
    input  logic clk_en_i,                      // Gates 'sys_clock_i' to advance CRTC state
    input  logic [DATA_WIDTH-1:0] data_i,       // Transfer data written from CPU to CRTC when CS asserted and /RW is low
    input  logic cs_i,                          // CRTC selected for data transfer (driven by address decoding)
    input  logic we_i,                          // Direction of date transfers (0 = reading from CRTC, 1 = writing to CRTC)
    input  logic rs_i,                          // Register select (0 = write address/read status, 1 = read addressed register)
    input  logic config_crt_i,                  // Select VDU (0 = 12"/CRTC, 1 = 9"/non-CRTC)

    output logic [ 7:0] r0_h_total_o,
    output logic [ 7:0] r1_h_displayed_o,
    output logic [ 7:0] r2_h_sync_pos_o,
    output logic [ 4:0] r3_h_sync_width_o,      // H/V-Sync extended from 4 to 5 bits to support 9-inch PET timings,
    output logic [ 4:0] r3_v_sync_width_o,      // which require longer sync pulses than the original CRTC can generate.
    output logic [ 6:0] r4_v_total_o,
    output logic [ 4:0] r5_v_adjust_o,
    output logic [ 6:0] r6_v_displayed_o,
    output logic [ 6:0] r7_v_sync_pos_o,
    output logic [ 4:0] r9_max_scan_line_o,
    output logic [13:0] r1213_start_addr_o
);
    // Storage required for all 32 addressable registers (R0..31)
    localparam integer unsigned CRTC_REG_COUNT_LOCAL = (1 << CRTC_ADDR_REG_WIDTH);

    logic [CRTC_ADDR_REG_WIDTH-1:0] ar = '0;                    // Address register used to select R0..31
    logic [DATA_WIDTH-1:0] r[CRTC_REG_COUNT_LOCAL-1:0];         // Storage for R0..31

    initial begin
        // North American 8032 60 Hz text-mode power-on state
        r[CRTC_R0_H_TOTAL]           = 8'h31;
        r[CRTC_R1_H_DISPLAYED]       = 8'h28;
        r[CRTC_R2_H_SYNC_POS]        = 8'h29;
        r[CRTC_R3_SYNC_WIDTH]        = 8'h0f;
        r[CRTC_R4_V_TOTAL]           = 8'h20;
        r[CRTC_R5_V_ADJUST]          = 8'h03;
        r[CRTC_R6_V_DISPLAYED]       = 8'h19;
        r[CRTC_R7_V_SYNC_POS]        = 8'h1d;
        r[CRTC_R9_MAX_SCAN_LINE]     = 8'h09;
        r[CRTC_R12_START_ADDR_HI]    = 8'h10;    // TA12 inverts video (1 = normal, 0 = inverted)
        r[CRTC_R13_START_ADDR_LO]    = 8'h00;
    end

    // Wishbone peripheral always completes in a single cycle.
    assign wbp_stall_o = 1'b0;
    wire [CRTC_ADDR_REG_WIDTH-1:0] crtc_addr = wbp_addr_i[CRTC_ADDR_REG_WIDTH-1:0];

    always_ff @(posedge wb_clock_i) begin
        wbp_ack_o <= '0;
        if (wbp_sel_i && wbp_cycle_i && wbp_strobe_i) begin
            wbp_data_o <= r[crtc_addr];
            
            if (wbp_we_i) begin
                r[crtc_addr] <= wbp_data_i;
            end
            
            wbp_ack_o <= 1'b1;
        end else if (clk_en_i && cs_i && we_i) begin
            if (rs_i == '0) ar <= data_i[4:0];  // RS = 0: Write to address register (select R0..31)
            else r[ar] <= data_i;               // RS = 1: Write to currently addressed register
        end
    end

    always_ff @(posedge wb_clock_i) begin
        if (config_crt_i == CONFIG_CRT_FIXED) begin
            r0_h_total_o       <= 8'd63;
            r1_h_displayed_o   <= 8'd40;
            r2_h_sync_pos_o    <= 8'd48;
            r3_h_sync_width_o  <= 5'd24;
            r3_v_sync_width_o  <= 5'd20;
            r4_v_total_o       <= 7'd31;
            r5_v_adjust_o      <= 5'd04;
            r6_v_displayed_o   <= 7'd25;
            r7_v_sync_pos_o    <= 7'd28;
            r9_max_scan_line_o <= 5'd07;
            r1213_start_addr_o <= 14'h1000;
        end else begin
            r0_h_total_o        <= r[CRTC_R0_H_TOTAL];
            r1_h_displayed_o    <= r[CRTC_R1_H_DISPLAYED];
            r2_h_sync_pos_o     <= r[CRTC_R2_H_SYNC_POS];
            r3_h_sync_width_o   <= { 1'b0, r[CRTC_R3_SYNC_WIDTH][3:0] };
            r3_v_sync_width_o   <= r[CRTC_R3_SYNC_WIDTH][7:4] == 0  // Per Datasheet, when bits 4-7 are all
                                    ? 5'h10                         // "0", VSYNC will be 16 scan lines wide.
                                    : { 1'b0, r[CRTC_R3_SYNC_WIDTH][7:4] };
            r4_v_total_o        <= r[CRTC_R4_V_TOTAL][6:0];
            r5_v_adjust_o       <= r[CRTC_R5_V_ADJUST][4:0];
            r6_v_displayed_o    <= r[CRTC_R6_V_DISPLAYED][6:0];
            r7_v_sync_pos_o     <= r[CRTC_R7_V_SYNC_POS][6:0];
            r9_max_scan_line_o  <= r[CRTC_R9_MAX_SCAN_LINE][4:0];
            r1213_start_addr_o  <= { r[CRTC_R12_START_ADDR_HI][5:0], r[CRTC_R13_START_ADDR_LO] };
        end
    end
endmodule
