DLehenbauer/econopet/gw/EconoPET/src/io.sv

// SPDX-License-Identifier: CC0-1.0
// https://github.com/dlehenbauer/econopet

import common_pkg::*;

// This module tracks and intercepts select reads/writes to I/O registers.
// This is used to inject USB keyboard input.
module io(
    input  logic                     wb_clock_i,

    input  logic                     cpu_be_i,
    input  logic                     cpu_wr_strobe_i,
    input  logic [   DATA_WIDTH-1:0] cpu_data_i,
    output logic [   DATA_WIDTH-1:0] cpu_data_o,
    output logic                     cpu_data_oe,   // Asserted when intercepting CPU read
    input  logic                     cpu_we_i,

    input  logic                     pia1_cs_i,     // PIA1 chip select (from address_decoding)
    input  logic                     pia2_cs_i,     // PIA2 chip select (from address_decoding)
    input  logic                     via_cs_i,      // VIA chip select (from address_decoding)
    input  logic [ VIA_RS_WIDTH-1:0] rs_i,          // Register select (cpu_addr[3:0])

    input  logic [KBD_COL_COUNT-1:0][KBD_ROW_COUNT-1:0] usb_kbd_i  // State of USB keyboard matrix
);
    // Map PIA and VIA registers to a contiguous address space.
    logic [IO_REG_ADDR_WIDTH-1:0] io_reg_addr;
    wire [PIA_RS_WIDTH-1:0] pia_rs = rs_i[PIA_RS_WIDTH-1:0];    // PIA register select is A[1:0]
    wire [VIA_RS_WIDTH-1:0] via_rs = rs_i[VIA_RS_WIDTH-1:0];    // VIA register select is A[3:0]
    
    always_comb begin
        unique case (1'b1)
            pia1_cs_i: io_reg_addr = { REG_IO_PIA1, pia_rs };
            pia2_cs_i: io_reg_addr = { REG_IO_PIA2, pia_rs };
            via_cs_i:  io_reg_addr = { REG_IO_VIA,  via_rs };
            default:   io_reg_addr = 'x;
        endcase
    end

    // CPU writes to I/O registers are cached here.
    logic [IO_REG_COUNT-1:0][DATA_WIDTH-1:0]          register          = '0;
    logic [PIA1_PORTA_KEY_D_OUT:PIA1_PORTA_KEY_A_OUT] selected_col      = '0;
    logic [KBD_ROW_COUNT-1:0]                         selected_row_data = '1;

    wire io_access = pia1_cs_i || pia2_cs_i || via_cs_i;
    wire cpu_io_wr = io_access && cpu_wr_strobe_i;

    always_ff @(posedge wb_clock_i) begin
        if (cpu_io_wr) begin
            register[io_reg_addr] <= cpu_data_i;
        end else begin
            // To relax timing, we pipeline reads from the 'register' array.
            selected_row_data <= usb_kbd_i[selected_col];
            selected_col <= register[REG_IO_PIA1_PORTA][PIA1_PORTA_KEY_D_OUT:PIA1_PORTA_KEY_A_OUT];
        end
    end

    always_ff @(posedge wb_clock_i) begin   
        cpu_data_oe <= 1'b0;

        if (cpu_be_i && !cpu_we_i) begin
            // Intercept CPU reads from select I/O registers.
            unique case (1'b1)
                pia1_cs_i: begin
                    unique case (pia_rs)
                        // Inject USB keyboard input by intercepting reads from PIA1_PORTB when
                        // a USB keyboard key is pressed.
                        PIA_PORTB: begin
                            cpu_data_o  <= selected_row_data;             // Load USB keyboard column into 'cpu_data_o' register.
                            cpu_data_oe <= selected_row_data != 8'hff;    // But only assert 'cpu_data_oe' if a key is pressed.
                        end
                        default: /* do nothing */;
                    endcase
                end
                default: /* do nothing */;
            endcase
        end
    end
endmodule
