DLehenbauer/econopet/gw/EconoPET/src/wbc_mux.sv

// SPDX-License-Identifier: CC0-1.0
// https://github.com/dlehenbauer/econopet

import common_pkg::*;

/**
 * Wishbone controller multiplexer.
 *
 * Multiplexes requests from multiple Wishbone controllers onto a shared bus.
 *
 * @param COUNT Number of Wishbone controllers
 */
module wbc_mux #(
    parameter COUNT = 2  // Number of Wishbone controllers
) (
    input logic wb_clock_i,  // Clock

    // Wishbone controllers to demux
    // (See https://cdn.opencores.org/downloads/wbspec_b4.pdf)
    input  logic [COUNT-1:0]                    wbc_cycle_i,
    input  logic [COUNT-1:0]                    wbc_strobe_i,
    input  logic [COUNT-1:0][WB_ADDR_WIDTH-1:0] wbc_addr_i,
    output logic [COUNT-1:0][   DATA_WIDTH-1:0] wbc_din_o,      // Peripheral -> Controller (WE=0)
    input  logic [COUNT-1:0][   DATA_WIDTH-1:0] wbc_dout_i,     // Controller -> Peripheral (WE=1)
    input  logic [COUNT-1:0]                    wbc_we_i,
    output logic [COUNT-1:0]                    wbc_stall_o,
    output logic [COUNT-1:0]                    wbc_ack_o,

    // Wishbone bus
    // (See https://cdn.opencores.org/downloads/wbspec_b4.pdf)
    output logic                     wb_cycle_o,
    output logic                     wb_strobe_o,
    output logic [WB_ADDR_WIDTH-1:0] wb_addr_o,
    input  logic [   DATA_WIDTH-1:0] wb_din_i,                  // Peripheral -> Controller (WE=0)
    output logic [   DATA_WIDTH-1:0] wb_dout_o,                 // Controller -> Peripheral (WE=1)
    output logic                     wb_we_o,
    input  logic                     wb_stall_i,
    input  logic                     wb_ack_i,

    // Control signals
    input logic [$clog2(COUNT)-1:0] wbc_grant_i, // Select controller
    input logic wbc_grant_valid_i                // (0 = stall new requests, 1 = admit new requests)
);
    always_comb begin
        // Peripheral receives inputs from the selected controller
        wb_cycle_o  = wbc_cycle_i[wbc_grant_i];
        wb_addr_o   = wbc_addr_i[wbc_grant_i];
        wb_dout_o   = wbc_dout_i[wbc_grant_i];
        wb_we_o     = wbc_we_i[wbc_grant_i];

        // Deasserting 'wbc_grant_valid_i' prevents new requests from being admitted by blocking the outgoing
        // strobe signal and returning a stall signal to the selected controller (below).
        wb_strobe_o = wbc_grant_valid_i & wbc_strobe_i[wbc_grant_i];

        for (int i = 0; i < COUNT; i = i + 1) begin
            wbc_din_o[i] = wb_din_i;

            if (i[$bits(wbc_grant_i)-1:0] == wbc_grant_i) begin
                // Deliver stall and ack signals to selected controller.
                wbc_stall_o[i] = !wbc_grant_valid_i || wb_stall_i;
                wbc_ack_o[i]   = wb_ack_i;
            end else begin
                // All other controllers are stalled and do not receive ack for current cycle.
                // We assert stall even if there is no active request.
                wbc_stall_o[i] = 1'b1;
                wbc_ack_o[i]   = 1'b0;
            end
        end
    end
endmodule
