DLehenbauer/econopet/fw/src/pet.c

// SPDX-License-Identifier: CC0-1.0
// https://github.com/dlehenbauer/econopet

#include "pch.h"
#include "pet.h"

#include "driver.h"
#include "ieee/ieee_drive.h"
#include "system_state.h"
#include "usb/keyboard.h"

void pet_reset() {
    // Per the W65C02S datasheet (sections 3.10 - 3.11):
    //
    //  * The CPU requires a minimum of 2 clock cycles to reset.  The CPU clock is 1 MHz (1 us period).
    //  * Deasserting RDY prevents the CPU from advancing it's state on negative PHI2 edges.
    // 
    // (See: https://www.westerndesigncenter.com/wdc/documentation/w65c02s.pdf)

    // Out of paranoia, deassert CPU 'reset' to ensure the CPU observes a clean reset pulse.
    set_cpu(CPU_HALT);
    sleep_us(4);

    ieee_drive_reset();
    usb_keyboard_reset(&system_state);

    memset(system_state.video_char_buffer, 0x20, 0x800);            // Clear video character buffer
    memset(system_state.video_char_buffer + 0x800, 0x0f, 0x800);    // Set color buffer to white on black
    memset(pet_key_matrix, 0xff, sizeof(pet_key_matrix));           // Clear keyboard matrix
    memset(usb_key_matrix, 0xff, sizeof(usb_key_matrix));           // Clear USB keyboard matrix
    
    // Assert CPU 'reset' while execution remains suspended.
    set_cpu(CPU_RESET);
    sleep_us(4);
    
    // Finally, deassert CPU 'reset' and allow the CPU to execute instructions.
    set_cpu(CPU_READY);
}

void pet_nmi() {
    // Out of paranoia, deassert CPU 'NMI' to ensure the CPU observes a clean pulse.
    set_cpu(CPU_READY);
    sleep_us(4);
    
    // Assert CPU 'nmi'.
    set_cpu(CPU_READY | CPU_NMI);
    sleep_us(4);
    
    // Finally, deassert CPU 'NMI'.
    set_cpu(CPU_READY);
}
