DLehenbauer/econopet/gw/EconoPET/src/audio.sv

// SPDX-License-Identifier: CC0-1.0
// https://github.com/dlehenbauer/econopet

import common_pkg::*;

module delta_sigma_dac (
    input  logic               clk_i,
    input  logic               reset_i,
    input  logic signed [15:0] dac_i,
    output logic               dac_o
);
    // Convert signed 16-bit input to unsigned biased.
    wire  [15:0] u16 = dac_i + 16'h8000;
    logic [16:0] accumulator = '0;

    always_ff @(posedge clk_i) begin
        if (reset_i) begin
            accumulator <= '0;
        end else begin
            // Add the current desired output 'u16' to the accumulator's lower 16 bits.
            accumulator <= accumulator[15:0] + u16;
        end
    end

    // If the accumulator's MSB is set, output a 1 to increase the output voltage.
    // Otherwise, output a 0 to decrease the output voltage.
    assign dac_o = accumulator[16];
endmodule

module audio (
    input  logic                          reset_i,
    input  logic                          sys_clock_i,
    input  logic                          clk1_en_i,
    input  logic                          sid_en_i,
    input  logic                          cpu_wr_strobe_i,
    input  logic [SID_ADDR_REG_WIDTH-1:0] addr_i,
    input  logic [                   7:0] data_i,       // writing to SID
    output logic [                   7:0] data_o,       // reading from SID

    input  logic diag_i,        // PIA1 PA7 pin 9: (0 = sound off, 1 = sound on)
    input  logic via_cb2_i,     // VIA CB2 pin 19: shift register used for 1-bit sound
    output logic audio_l_o,     // Audio left  : VIA CB2 mixed with SID output (1-bit ΔΣ-encoded)
    output logic audio_r_o      // Audio right : VIA CB2 mixed with SID output (1-bit ΔΣ-encoded)
);
    wire sid_wr_en = cpu_wr_strobe_i && sid_en_i;

    // See http://www.cbmhardware.de/show.php?r=14&id=71/PETSID
    logic signed [15:0] sid_out;

    sid #(
        .POT_SUPPORT(0)
    ) sid (
        .clk   (sys_clock_i),  // System clock
        .clkEn (clk1_en_i),    // 1 MHz clock enable
        .iRst  (reset_i),      // sync. reset (active high)
        .iWE   (sid_wr_en),    // write enable (active high)
        .iAddr (addr_i),       // sid address
        .iDataW(data_i),       // writing to SID
        .oDataR(data_o),       // reading from SID
        .oOut  (sid_out)       // sid output
`ifndef VERILATOR
        ,
        // IceSID excludes ioPotX/Y for verilator
        .ioPotX(),
        .ioPotY()
`endif
    );

    wire signed [15:0] cb2_out = via_cb2_i && diag_i ? 16'h800 : -16'h800;

    wire signed [15:0] mixed = sid_out + cb2_out;

    delta_sigma_dac dac (
        .clk_i  (sys_clock_i),
        .reset_i(reset_i),
        .dac_i  (mixed),
        .dac_o  (audio_l_o)
    );

    // For now, the left and right audio channels both emit the same 1-bit ΔΣ
    // encoded waveform.
    assign audio_r_o = audio_l_o;
endmodule
