DLehenbauer/econopet/fw/src/term_inject.h

// SPDX-License-Identifier: CC0-1.0
// https://github.com/dlehenbauer/econopet

#pragma once

#include <stdbool.h>

/**
 * Inject an ASCII character as a PET keystroke.
 * 
 * This function queues the character to be injected. The actual keystroke
 * injection happens during input_task() processing, which handles press/release
 * timing and syncs the keyboard matrix to the FPGA.
 * 
 * @param ch The ASCII character to inject (0-127)
 * @return true if the character was queued, false if queue is full or char unsupported
 */
bool term_inject_char(int ch);

/**
 * Process pending keystroke injections.
 * 
 * This function should be called from input_task() to handle the timing of
 * key press and release events. It modifies usb_key_matrix and relies on
 * sync_state() being called afterward to send the matrix to the FPGA.
 */
void term_inject_task(void);
