DLehenbauer/econopet/gw/EconoPET/sim/superpet_top_tb.sv

// SPDX-License-Identifier: CC0-1.0
// https://github.com/dlehenbauer/econopet

`include "./sim/tb.svh"

import common_pkg::*;

// Standalone end-to-end smoke test for the SuperPET 6809 side.
//
// Deliberately does not reuse mock_system.sv/mock_cpu.sv (which drive the
// physical-6502 bus role via the m6502 soft core) -- in 6809 mode, the
// physical CPU is permanently tri-stated and the mc6809 core inside 'top'
// is the only active bus master, so there is nothing for a mock 6502 to
// drive. Instead this wires 'top' directly to mock_sram (a real,
// timing-accurate AS6C1008 model) and the SPI1 driver, mirroring
// mock_system.sv's non-CPU wiring.
module superpet_top_tb;
    // Phase 2 (below) validates full 16-bank $9000 switching. SRAM A12-A14
    // come from the shared bus (no dedicated FPGA pins), which main.sv
    // drives with the bank-translated address during the CPU window; the
    // ram_addr concatenation below mirrors that PCB wiring.

    bit sys_clock;
    clock_gen #(SYS_CLOCK_MHZ) sys_clock_gen (.clock_o(sys_clock));
    initial sys_clock_gen.start;

    logic [CPU_ADDR_WIDTH-1:0] bus_addr;
    wire  [DATA_WIDTH-1:0]     bus_data;
    logic bus_we_n;

    logic [DATA_WIDTH-1:0] bus_data_mux;
    logic                  bus_data_mux_oe;

    assign bus_data = bus_data_mux_oe ? bus_data_mux : {DATA_WIDTH{1'bz}};

    // Reset is a wire-OR net: the FPGA can assert it (top_reset_n/oe), and we
    // provide the external/manual side, exactly like mock_system.sv.
    bit   manual_reset_n = 1'b1;
    logic cpu_reset_n;
    logic top_reset_n;
    logic top_reset_n_oe;
    assign cpu_reset_n = top_reset_n_oe ? top_reset_n : manual_reset_n;

    logic cpu_be;
    logic cpu_clock;
    logic cpu_ready;

    logic [CPU_ADDR_WIDTH-1:0] top_addr;
    logic [CPU_ADDR_WIDTH-1:0] top_addr_oe;
    logic [DATA_WIDTH-1:0] top_data;
    logic [DATA_WIDTH-1:0] top_data_oe;
    logic top_we_n;
    logic top_we_n_oe;

    logic ram_addr_a10_o, ram_addr_a11_o, ram_addr_a15_o, ram_addr_a16_o;
    logic ram_oe_n_o, ram_we_n_o;
    logic io_oe_n, pia1_cs_n, pia2_cs_n, via_cs_n;

    logic spi_sck, spi_cs_n, spi_pico, spi_poci, spi_stall;
    logic [7:0] spi_rx_data;

    top top (
        .sys_clock_i(sys_clock),

        .cpu_be_o(cpu_be),
        .cpu_ready_o(cpu_ready),
        .cpu_reset_n_i(cpu_reset_n),
        .cpu_reset_n_o(top_reset_n),
        .cpu_reset_n_oe(top_reset_n_oe),
        .cpu_clock_o(cpu_clock),
        // Tied off, not fed from bus_addr: no physical CPU exists in this
        // bench, and the feedback (cpu_addr_o -> bus -> cpu_addr_i ->
        // active_cpu_addr mux) is a false combinational loop.
        .cpu_addr_i ({CPU_ADDR_WIDTH{1'b0}}),
        .cpu_addr_o (top_addr),
        .cpu_addr_oe(top_addr_oe),
        .cpu_data_i (bus_data),
        .cpu_data_o (top_data),
        .cpu_data_oe(top_data_oe),
        .cpu_we_n_i (1'b1),      // Physical CPU off-bus in 6809 mode
        .cpu_we_n_o (top_we_n),
        .cpu_we_n_oe(top_we_n_oe),

        // No physical CPU: tie the interrupt pads inactive. Left unconnected
        // these read 0 under Verilator, asserting IRQ to the soft core forever.
        .cpu_irq_n_i(1'b1),
        .cpu_nmi_n_i(1'b1),
        .cpu_sync_i(1'b0),

        .ram_addr_a10_o(ram_addr_a10_o),
        .ram_addr_a11_o(ram_addr_a11_o),
        .ram_addr_a15_o(ram_addr_a15_o),
        .ram_addr_a16_o(ram_addr_a16_o),
        .ram_oe_n_o(ram_oe_n_o),
        .ram_we_n_o(ram_we_n_o),
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
